takashicompany/tightwriter/images/build/IMG_2944.jpg

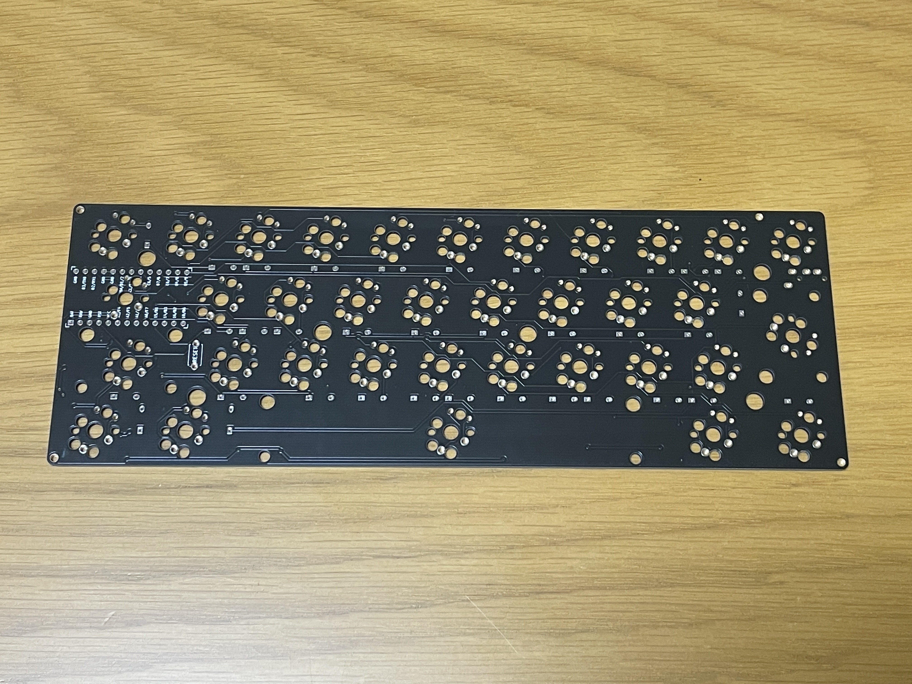
images/build/IMG_2944.jpg
