takashicompany/tightwriter/images/build/IMG_2945.jpg

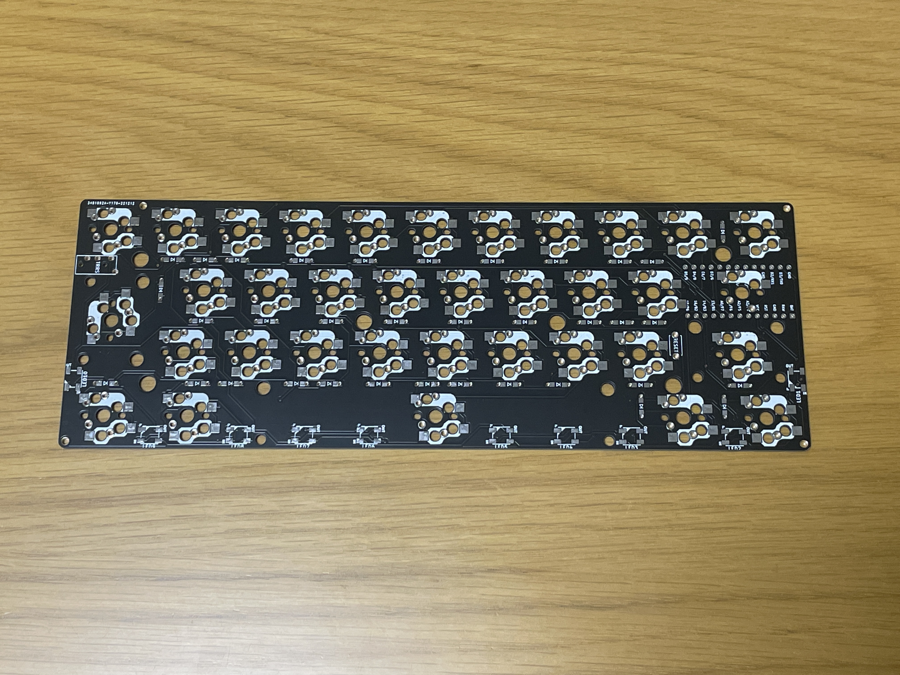
images/build/IMG_2945.jpg
