takashicompany/tightwriter/images/build/IMG_2948.jpg

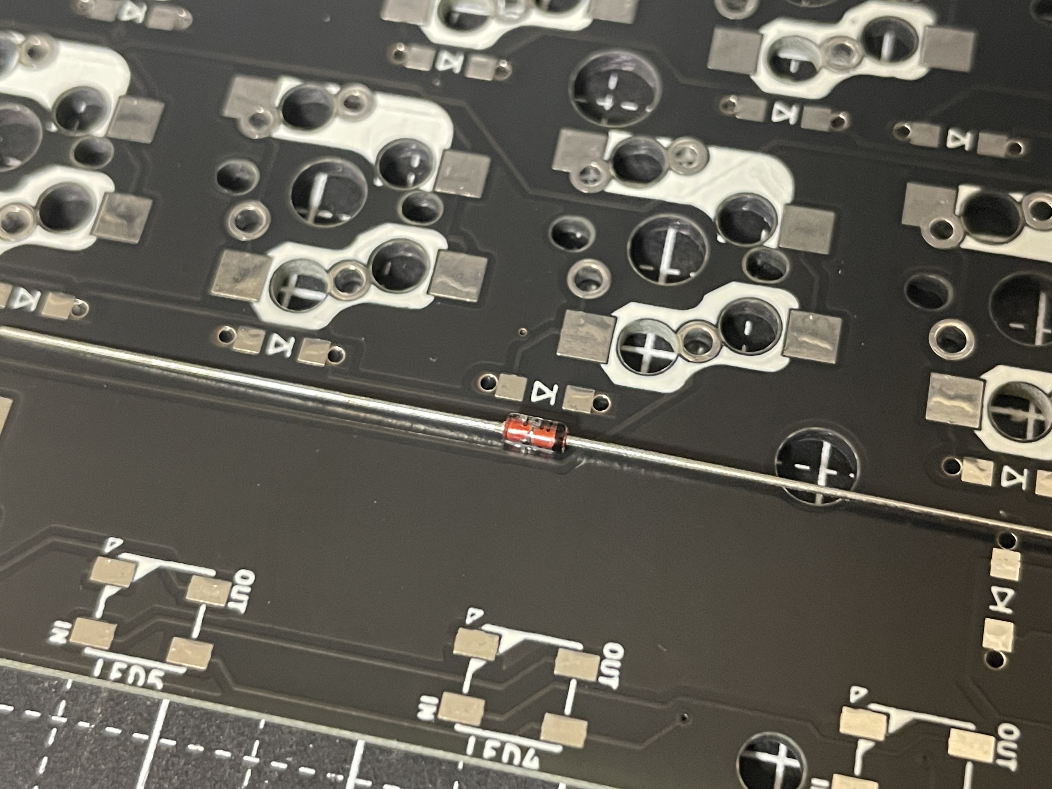
images/build/IMG_2948.jpg
