takashicompany/tightwriter/images/build/IMG_2955.jpg

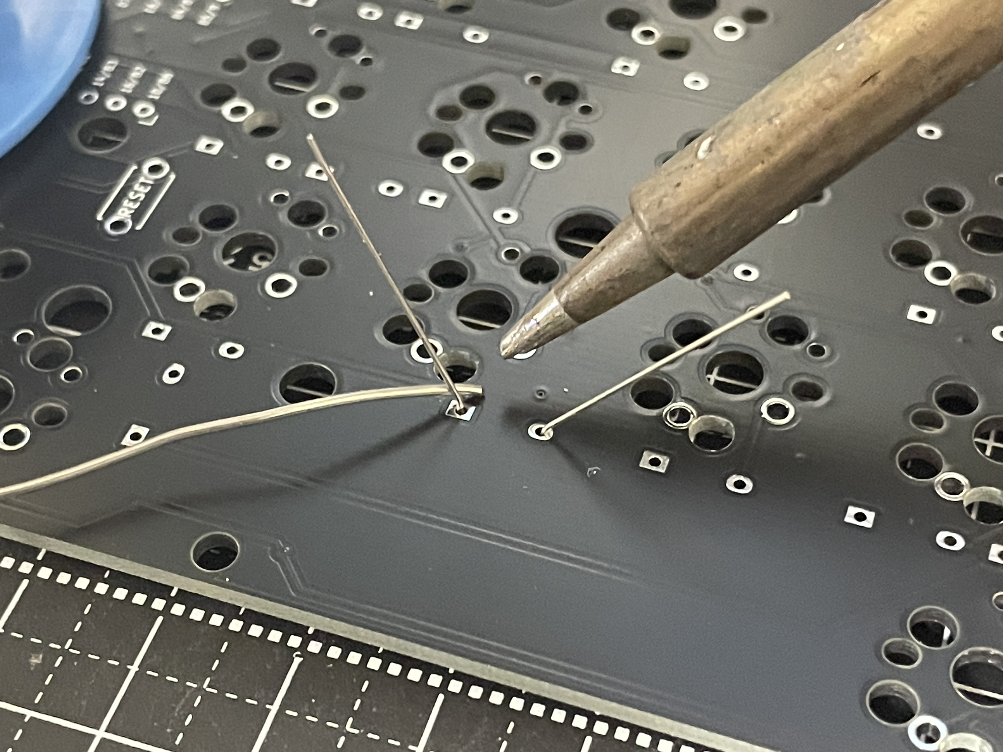
images/build/IMG_2955.jpg
