takashicompany/tightwriter/images/build/IMG_2965.jpg

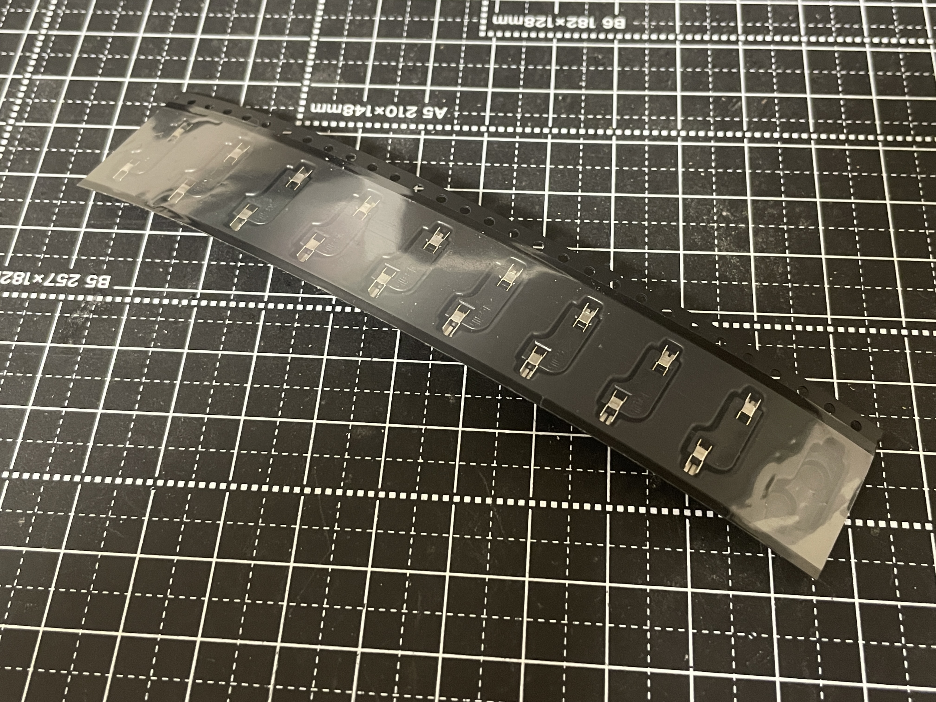
images/build/IMG_2965.jpg
