takashicompany/tightwriter/images/build/IMG_2968.jpg

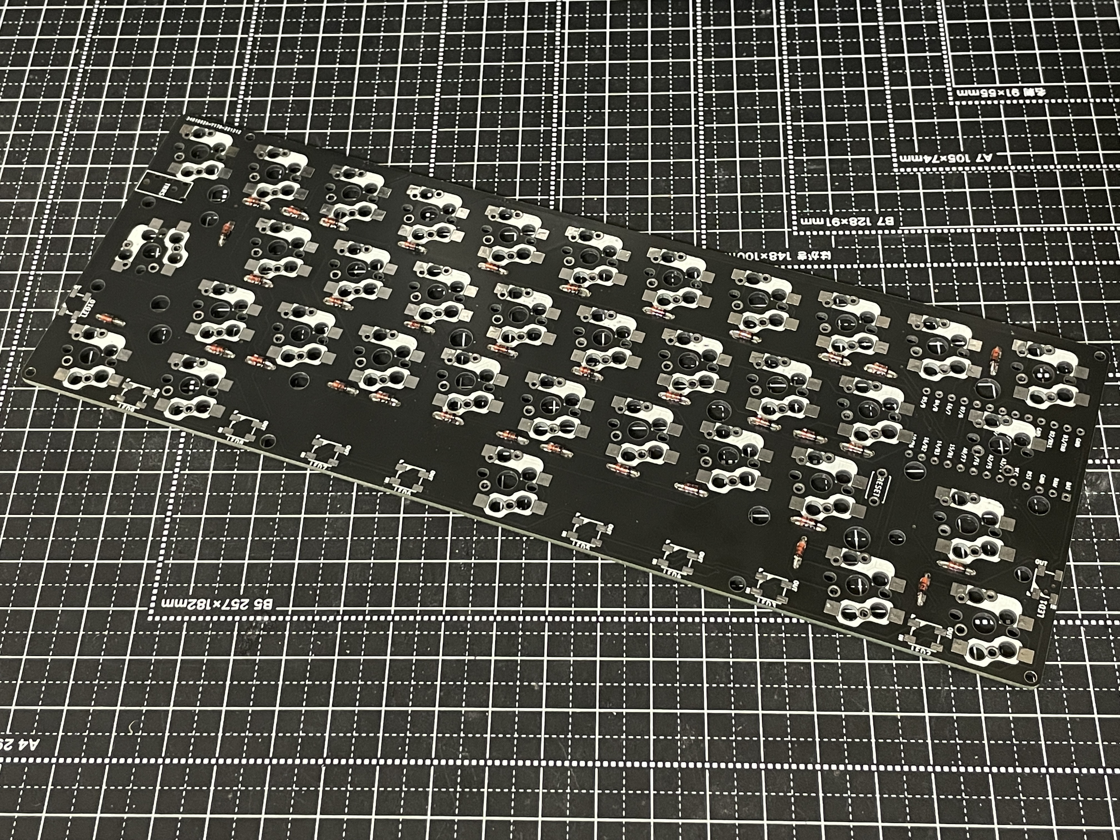
images/build/IMG_2968.jpg
