takashicompany/tightwriter/images/build/IMG_3021.jpg

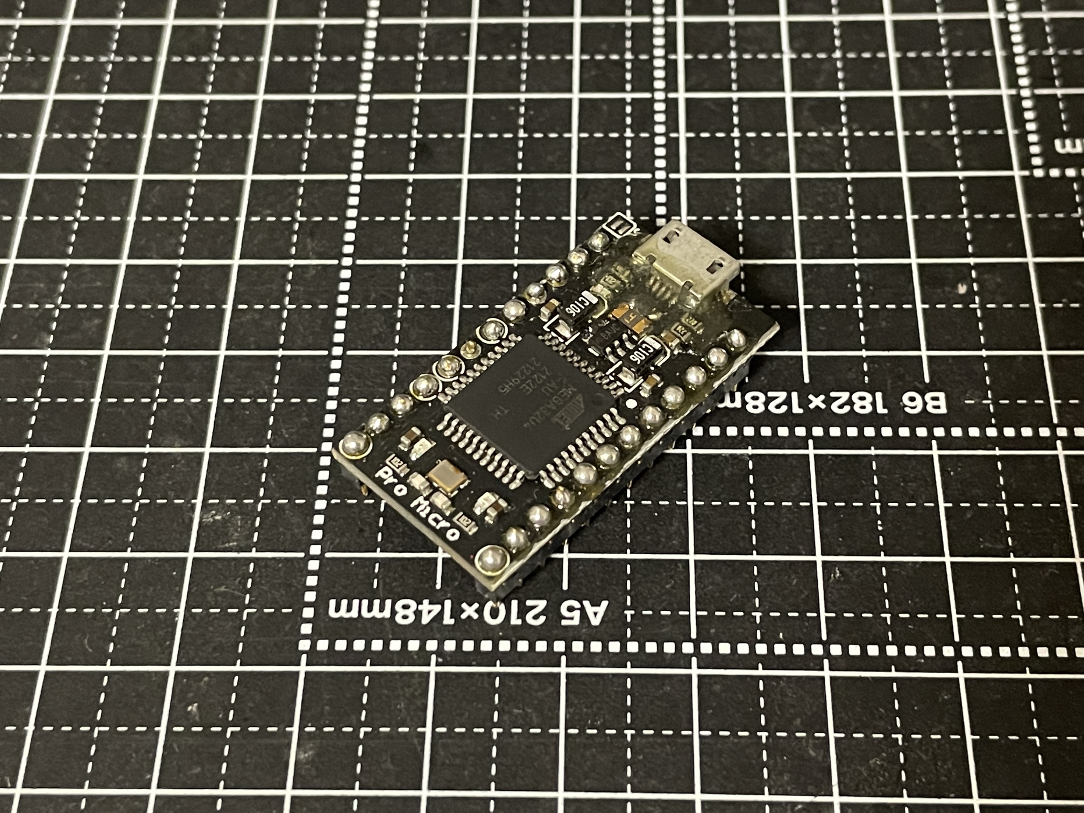
images/build/IMG_3021.jpg
