takashicompany/tightwriter/images/build/IMG_3022.jpg

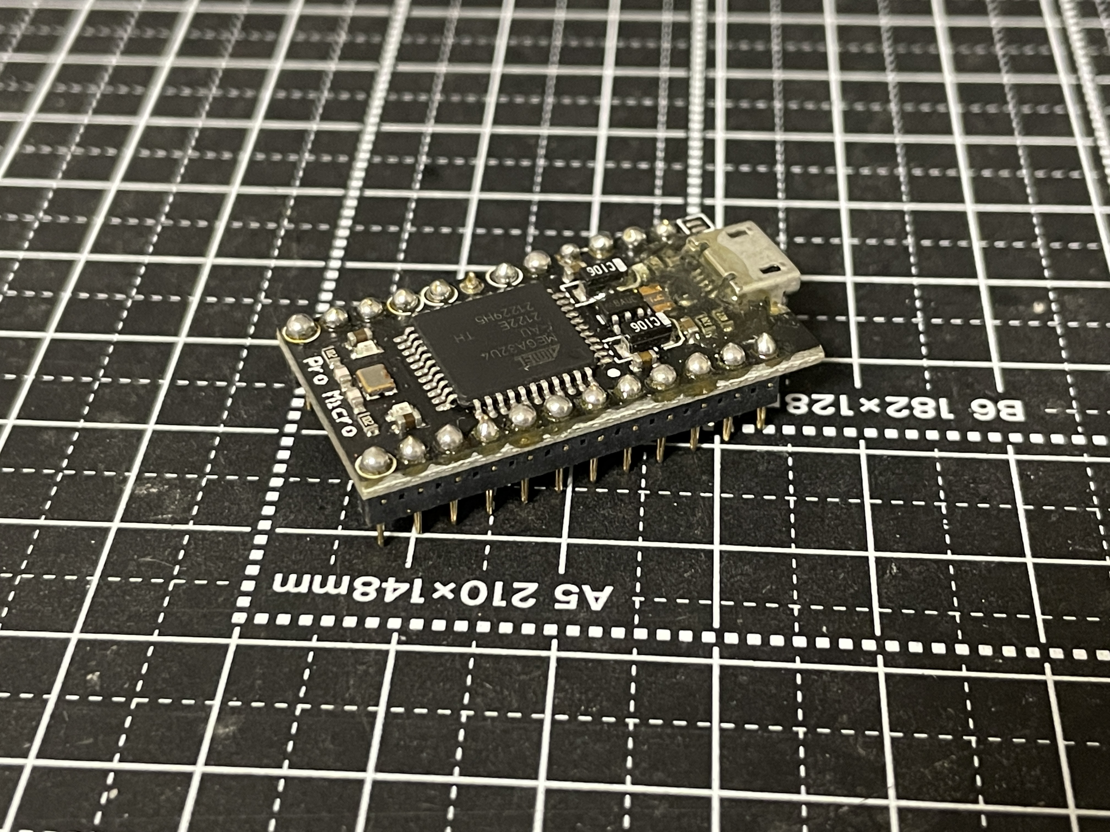
images/build/IMG_3022.jpg
