takashicompany/tightwriter/images/build/IMG_3026.jpg

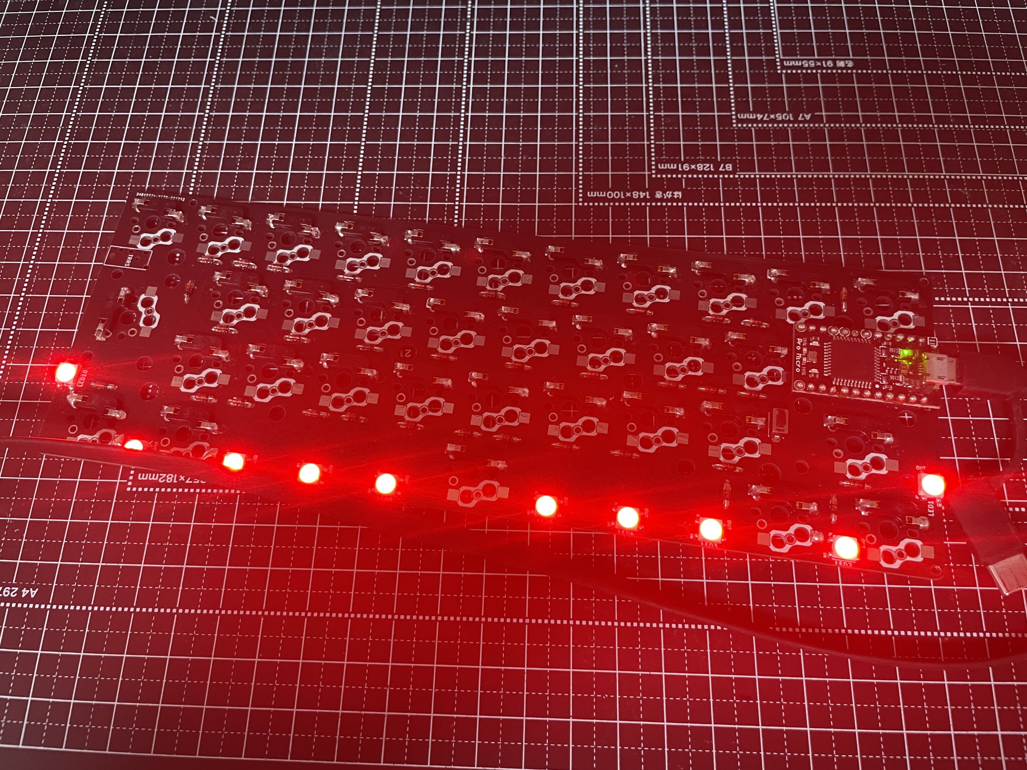
images/build/IMG_3026.jpg
