takashicompany/tightwriter/images/build/IMG_3027.jpg

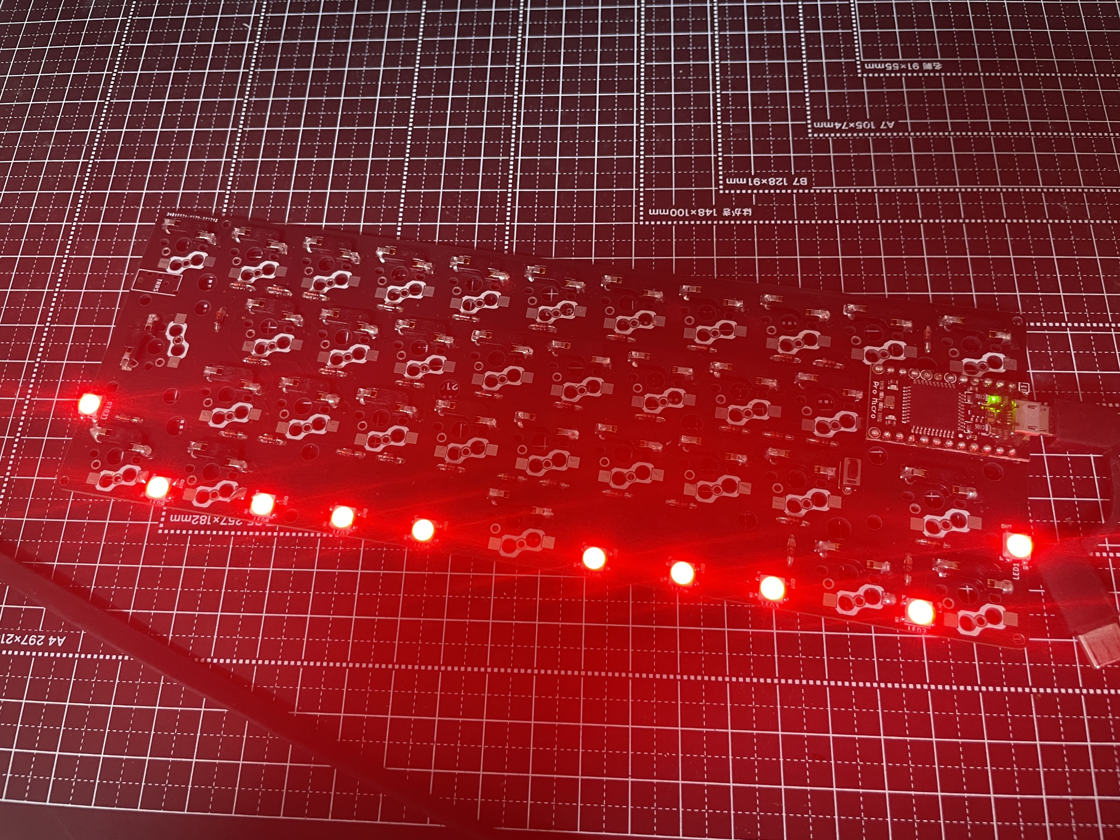
images/build/IMG_3027.jpg
