takashicompany/tightwriter/images/build/IMG_3028.jpg

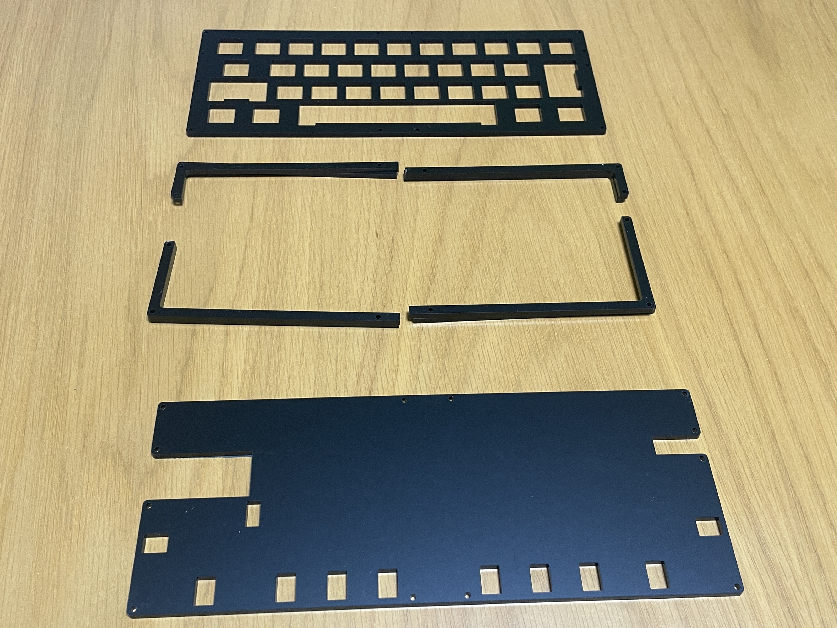
images/build/IMG_3028.jpg
