takashicompany/tightwriter/images/build/IMG_3031.jpg

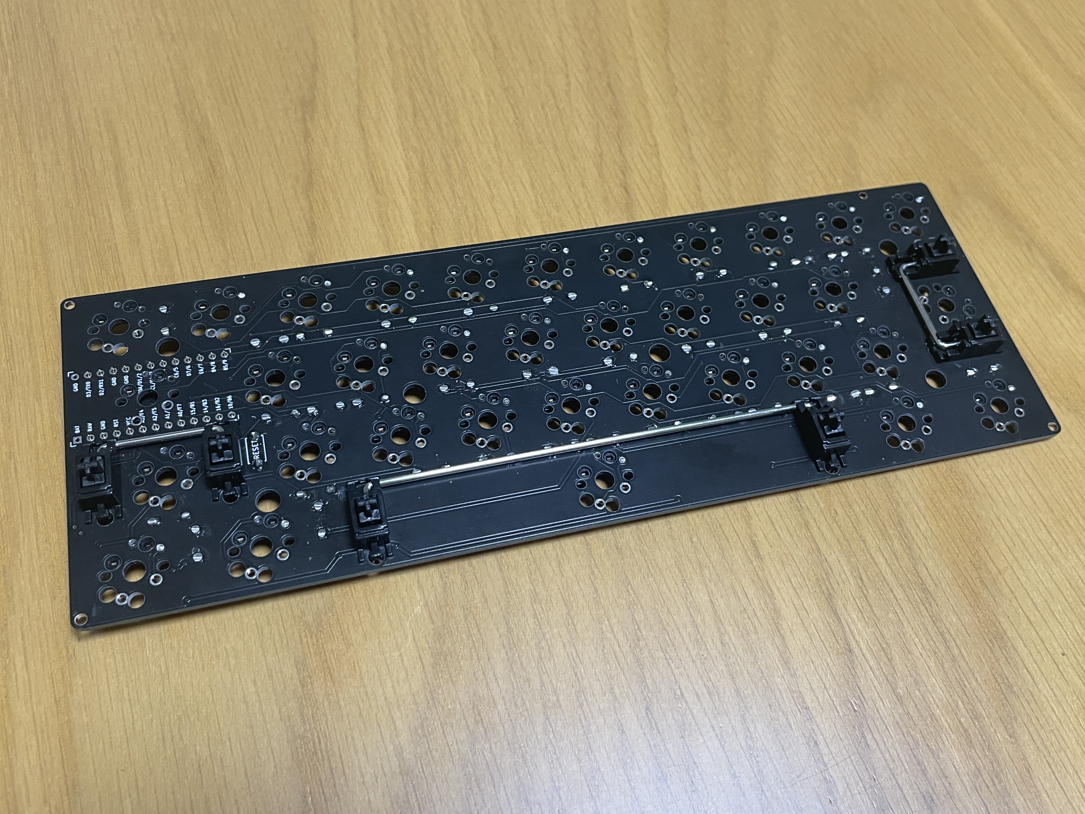
images/build/IMG_3031.jpg
