takashicompany/tightwriter/images/build/IMG_3033.jpg

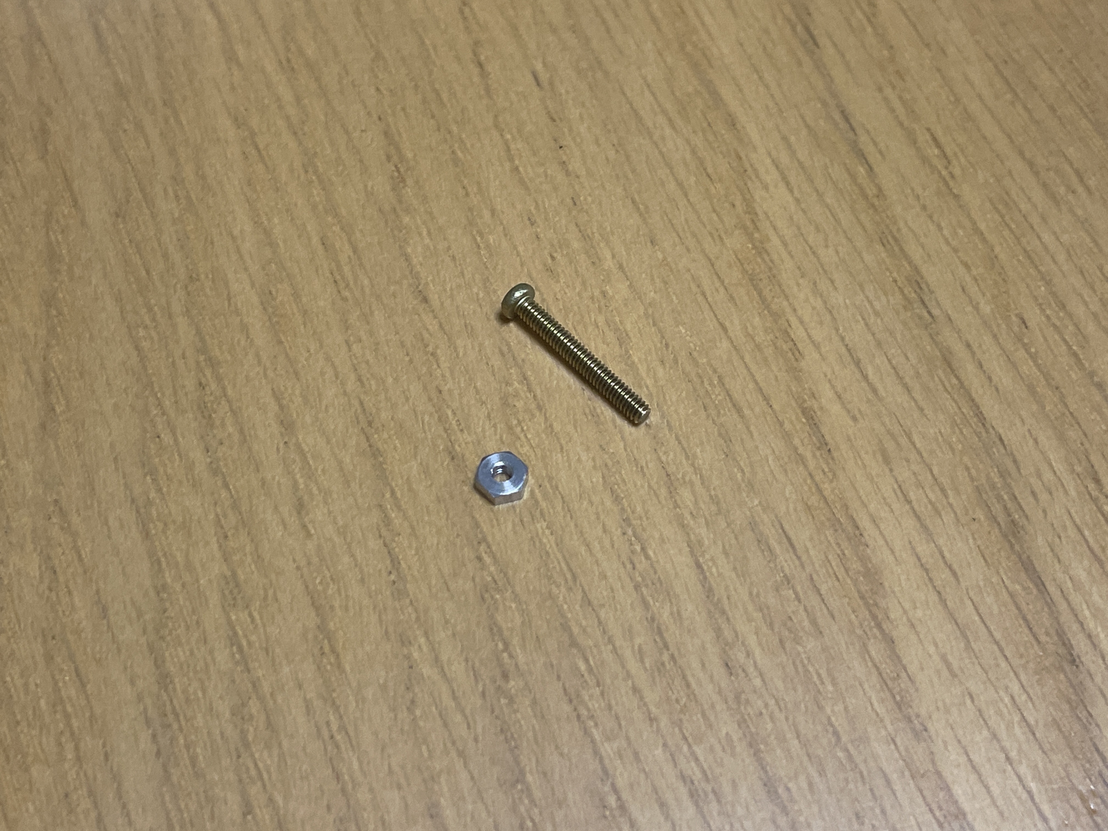
images/build/IMG_3033.jpg
