takashicompany/tightwriter/images/build/IMG_3039.jpg

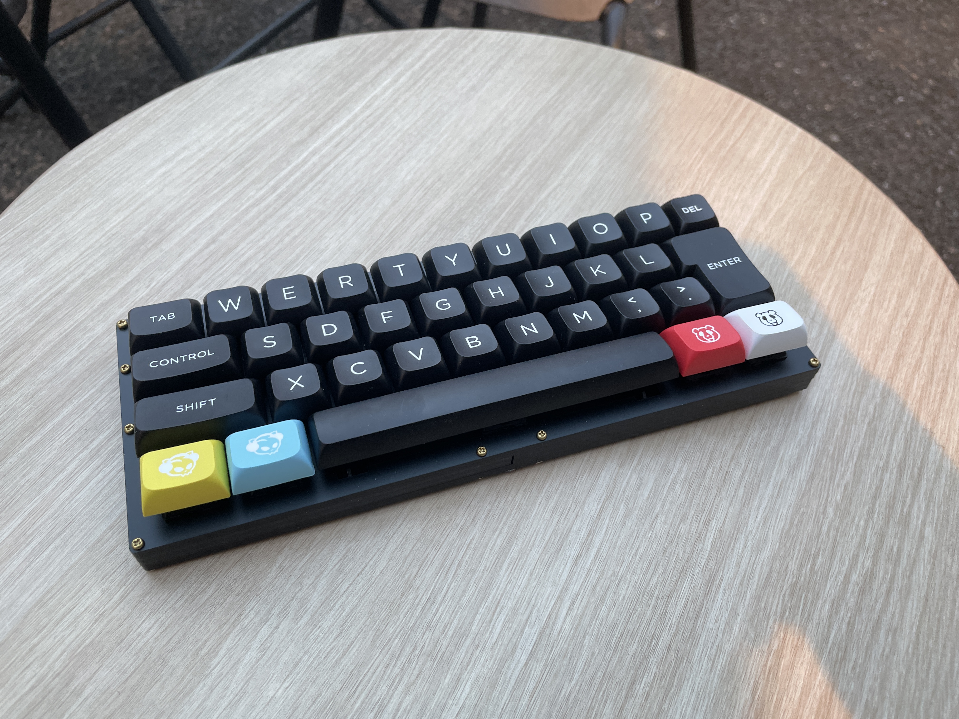
images/build/IMG_3039.jpg
