takashicompany/tightwriter/images/build/IMG_3040.jpg

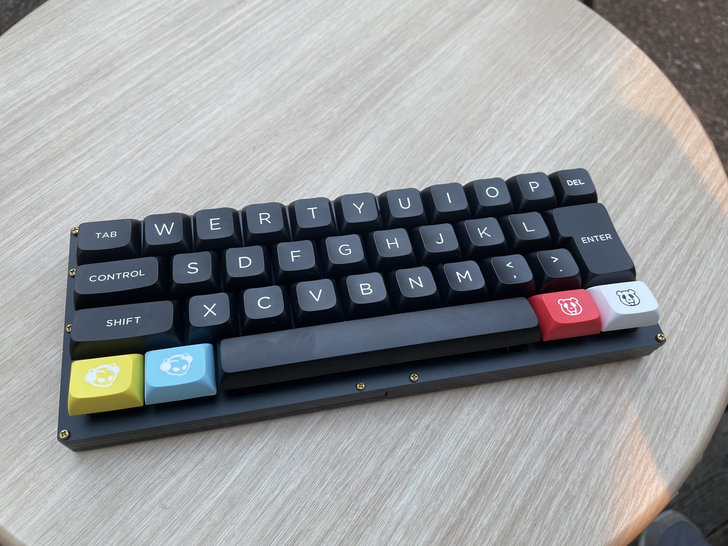
images/build/IMG_3040.jpg
