takashicompany/tightwriter/images/build/IMG_3042.jpg

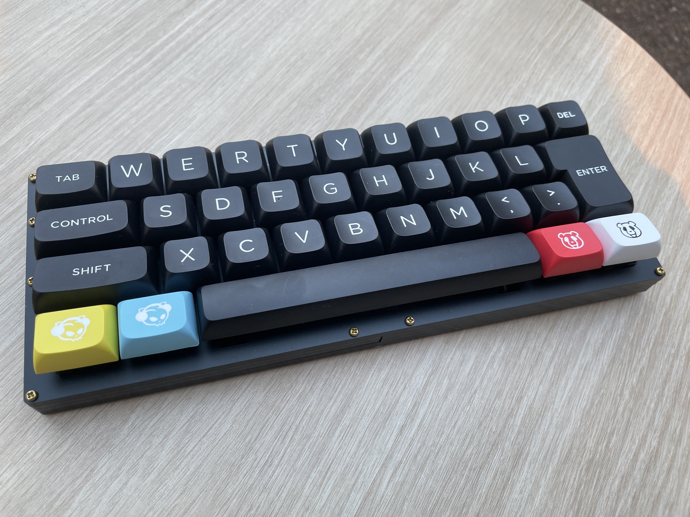
images/build/IMG_3042.jpg
