takashicompany/tightwriter/images/build/IMG_3043.jpg

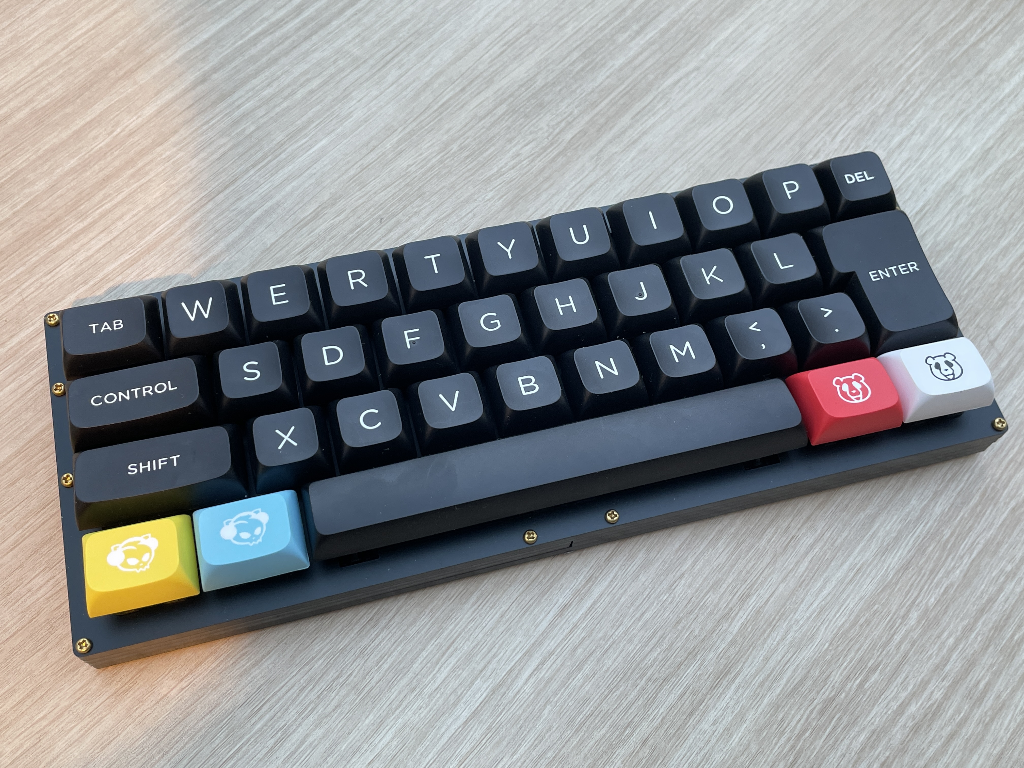
images/build/IMG_3043.jpg
