takashicompany/tightwriter/images/build/IMG_3044.jpg

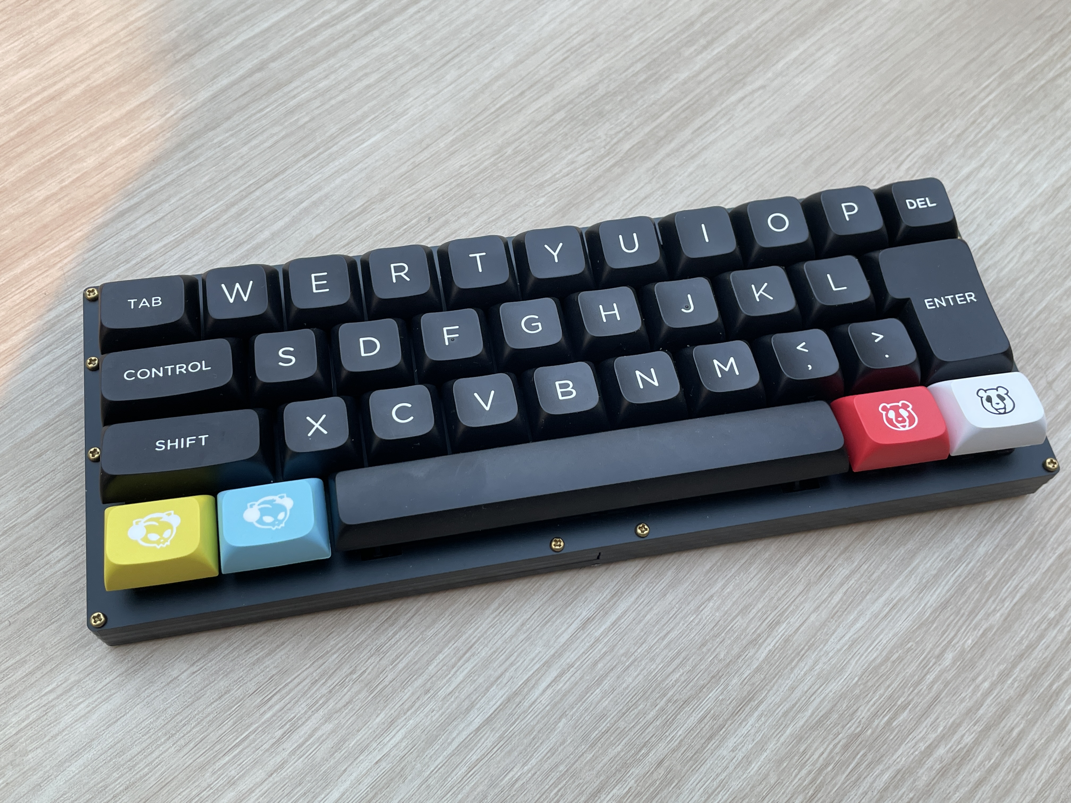
images/build/IMG_3044.jpg
