takashicompany/tightwriter/images/build/IMG_3045.jpg

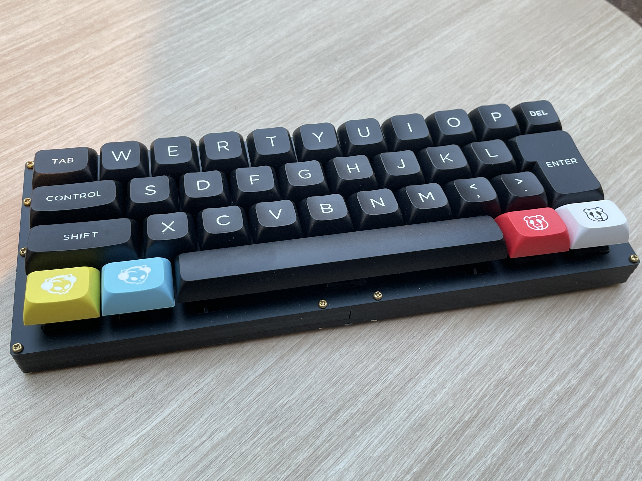
images/build/IMG_3045.jpg
