takashicompany/tightwriter/images/build/IMG_3057.jpg

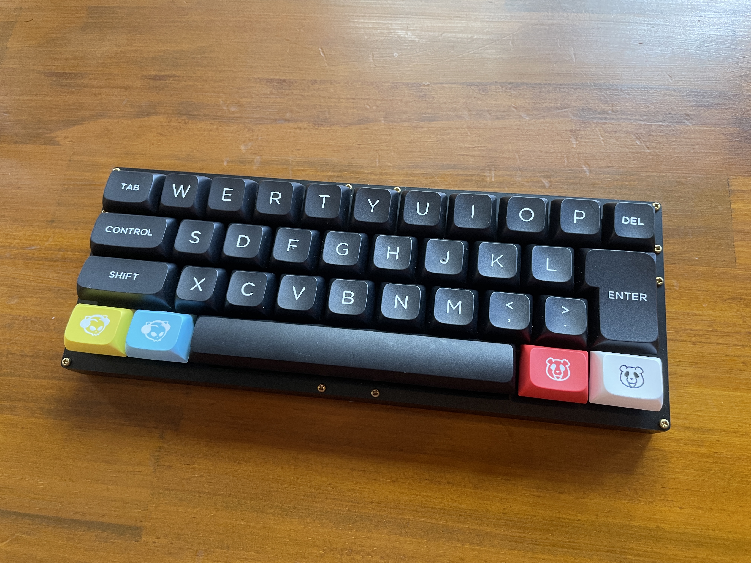
images/build/IMG_3057.jpg
