takashicompany/tightwriter/images/build/IMG_3058.jpg

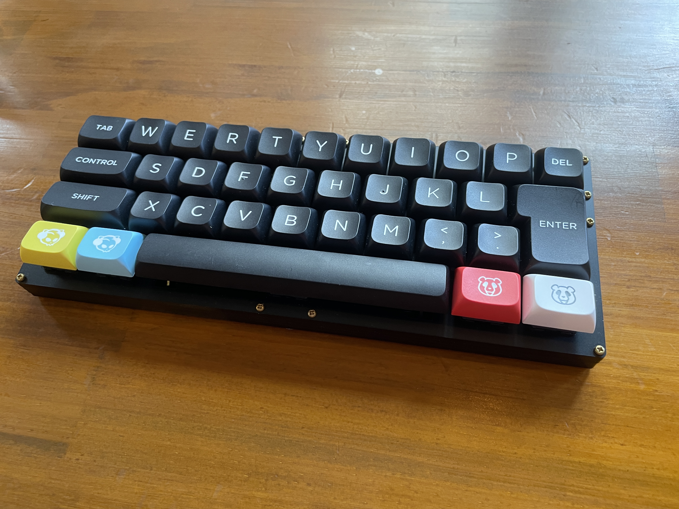
images/build/IMG_3058.jpg
