takashicompany/tightwriter/images/build/IMG_3059.jpg

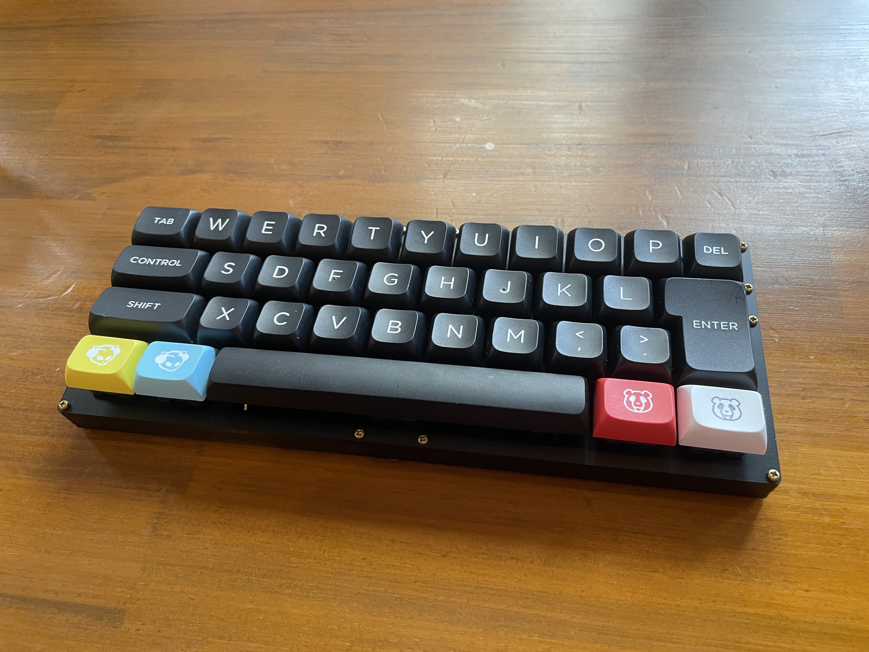
images/build/IMG_3059.jpg
