takashicompany/tightwriter/images/build/IMG_3060.jpg

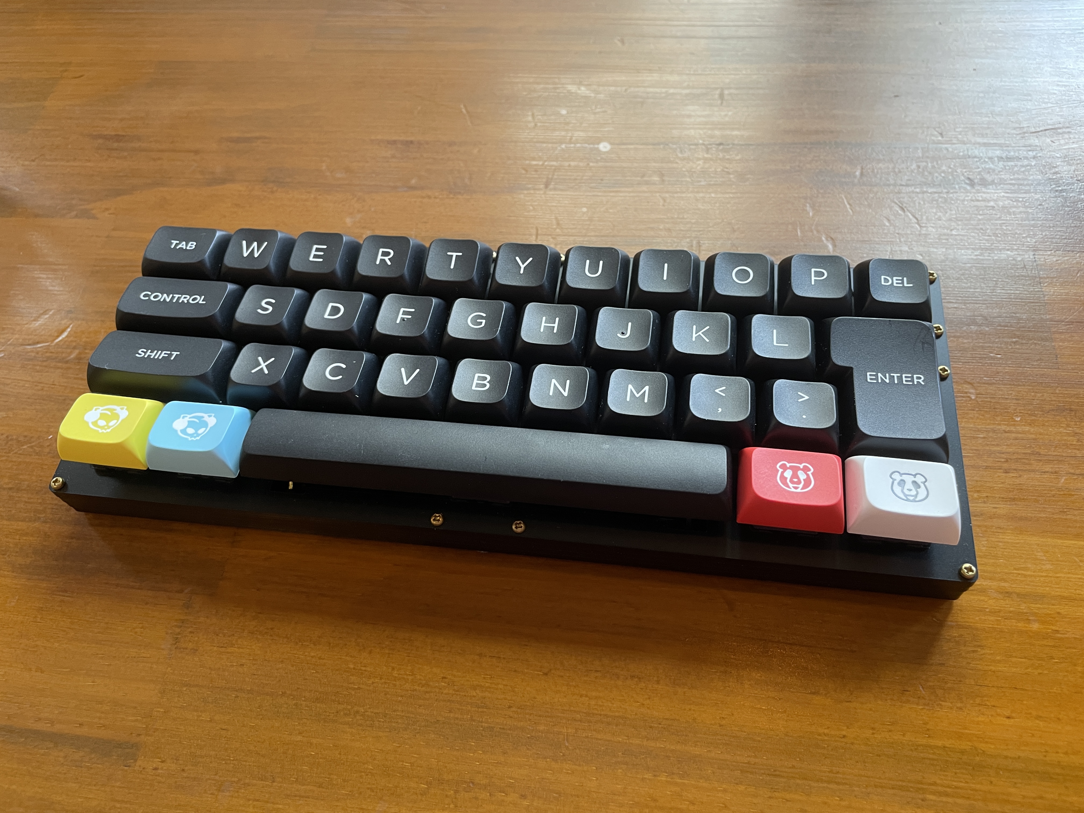
images/build/IMG_3060.jpg
