takashicompany/tightwriter/images/build/IMG_3132.jpg

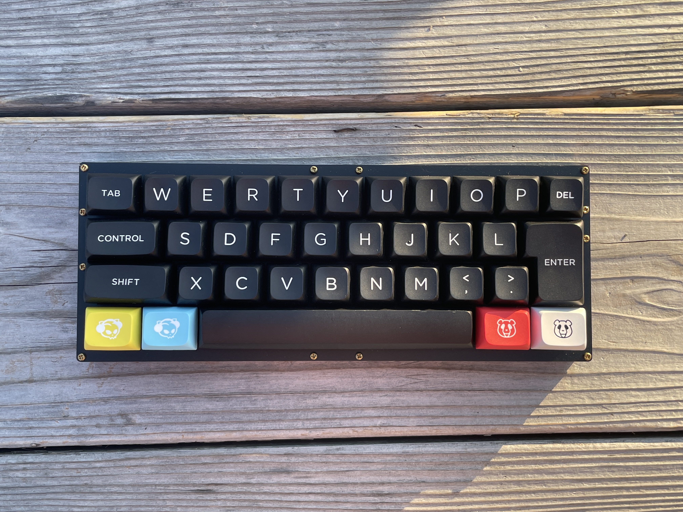
images/build/IMG_3132.jpg
