takashicompany/tightwriter/images/build/IMG_3134.jpg

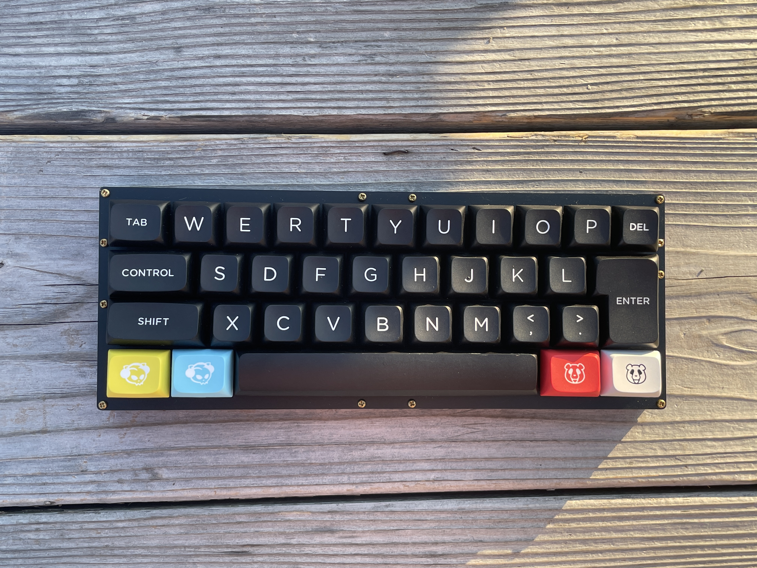
images/build/IMG_3134.jpg
