takashicompany/tightwriter/images/build/IMG_3135.jpg

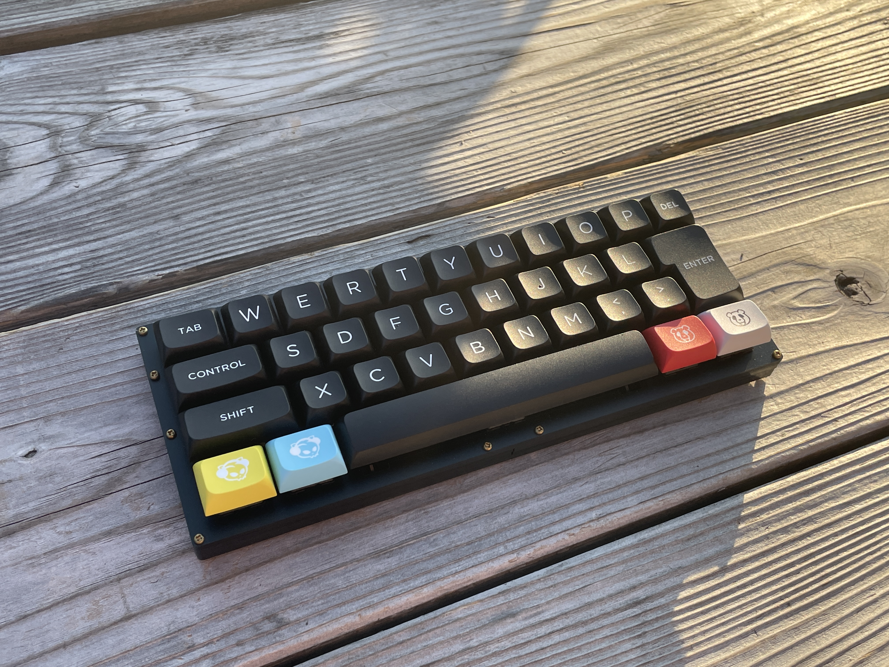
images/build/IMG_3135.jpg
