takashicompany/tightwriter/images/build/IMG_3136.jpg

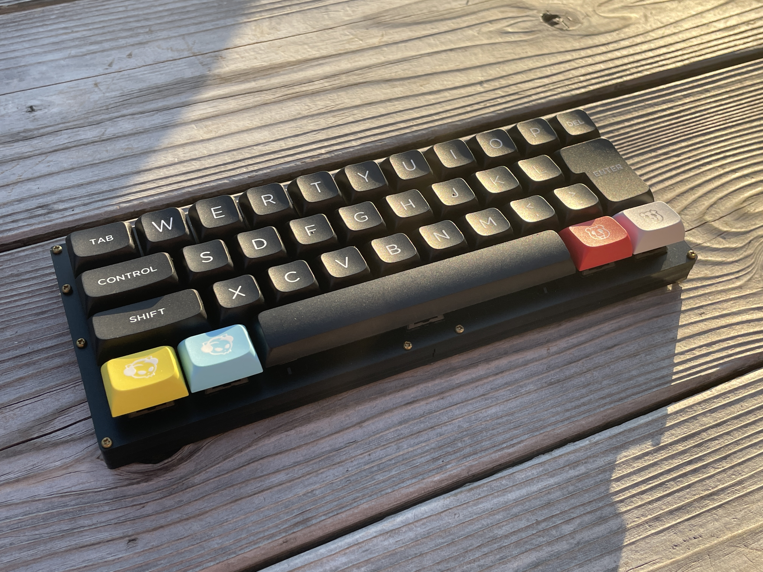
images/build/IMG_3136.jpg
