takashicompany/tightwriter/images/build/IMG_3137.jpg

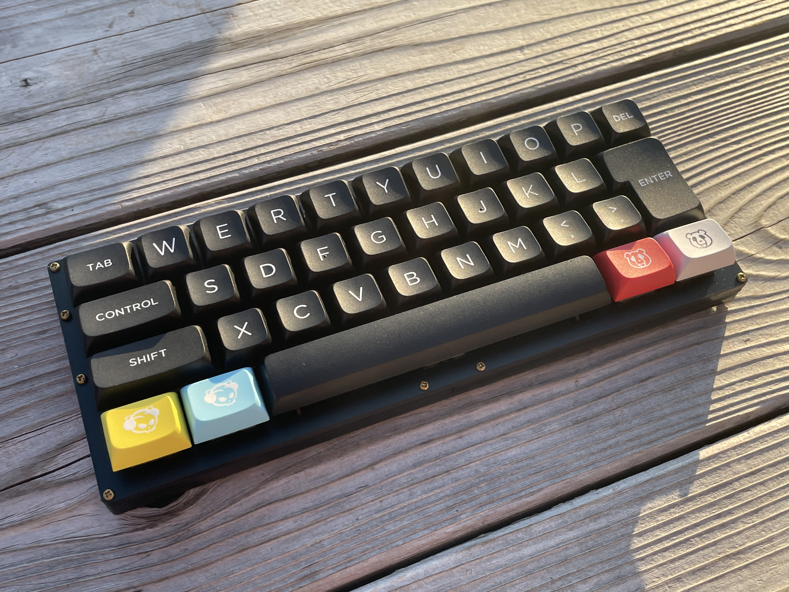
images/build/IMG_3137.jpg
