takashicompany/tightwriter/images/build/IMG_3139.jpg

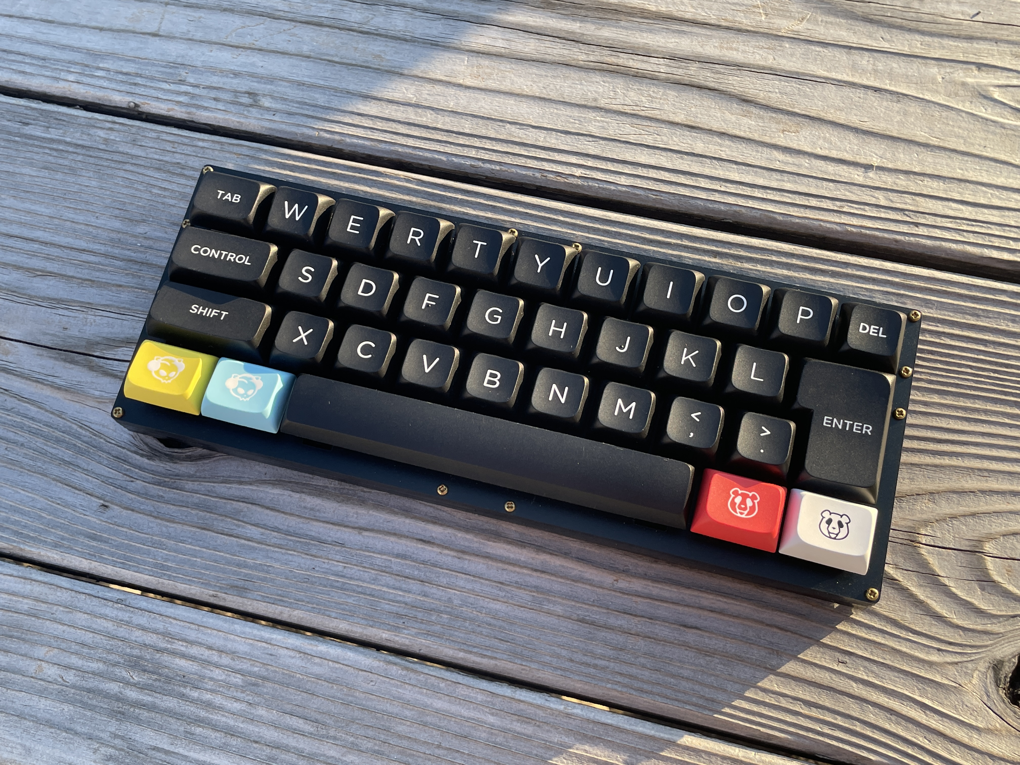
images/build/IMG_3139.jpg
