takashicompany/tightwriter/images/build/IMG_3140.jpg

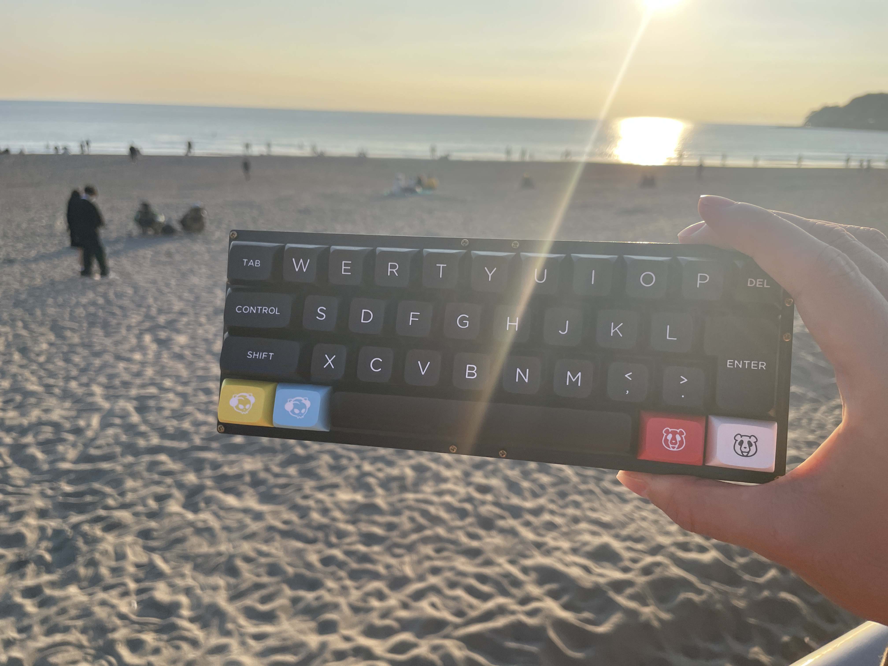
images/build/IMG_3140.jpg
