takashicompany/tightwriter/images/build/IMG_3141.jpg

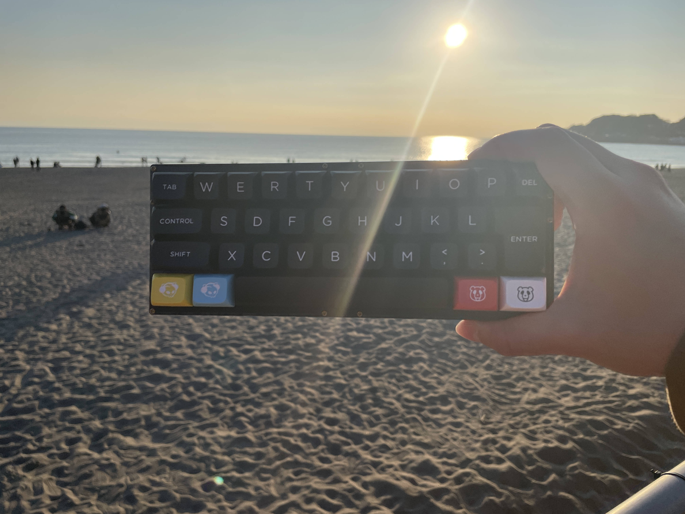
images/build/IMG_3141.jpg
