takashicompany/tightwriter/images/build/IMG_3142.jpg

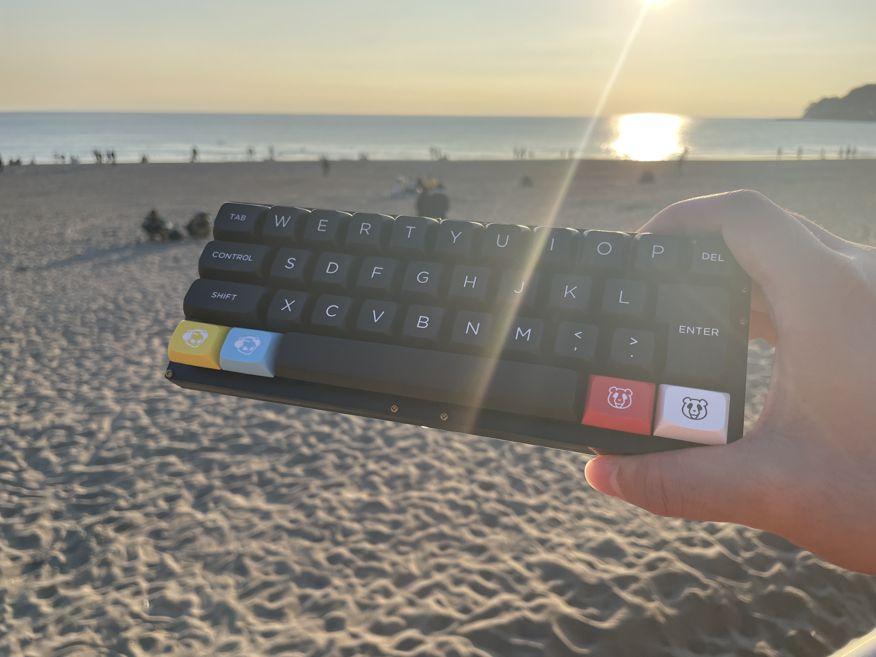
images/build/IMG_3142.jpg
