takashicompany/tightwriter/images/build/IMG_3144.jpg

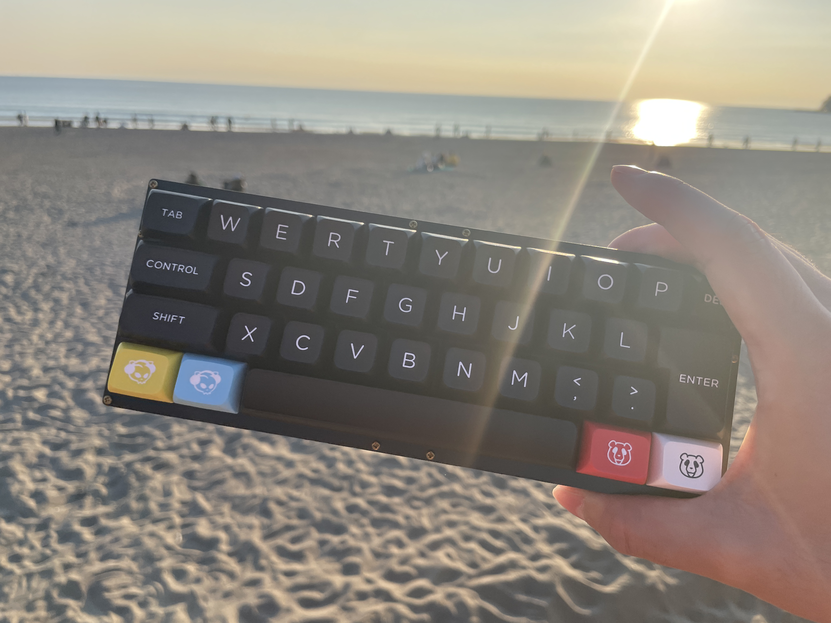
images/build/IMG_3144.jpg
