takashicompany/tightwriter/images/build/IMG_3145.jpg

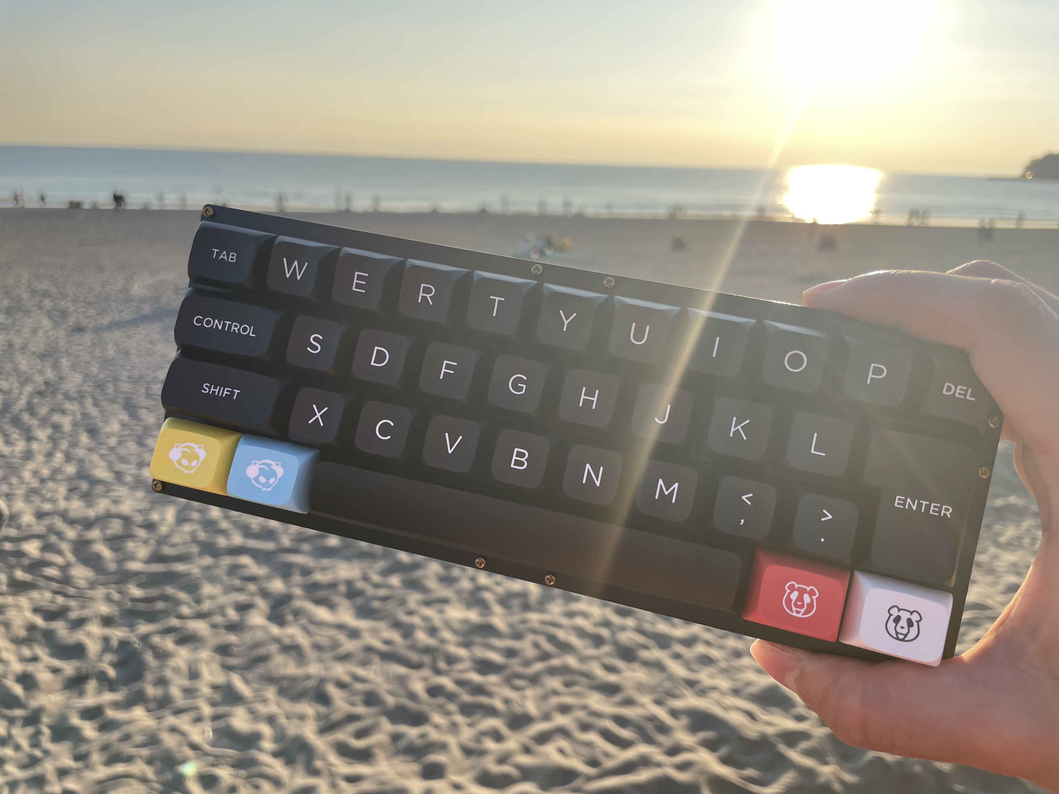
images/build/IMG_3145.jpg
