takashicompany/tightwriter/images/build/IMG_3146.jpg

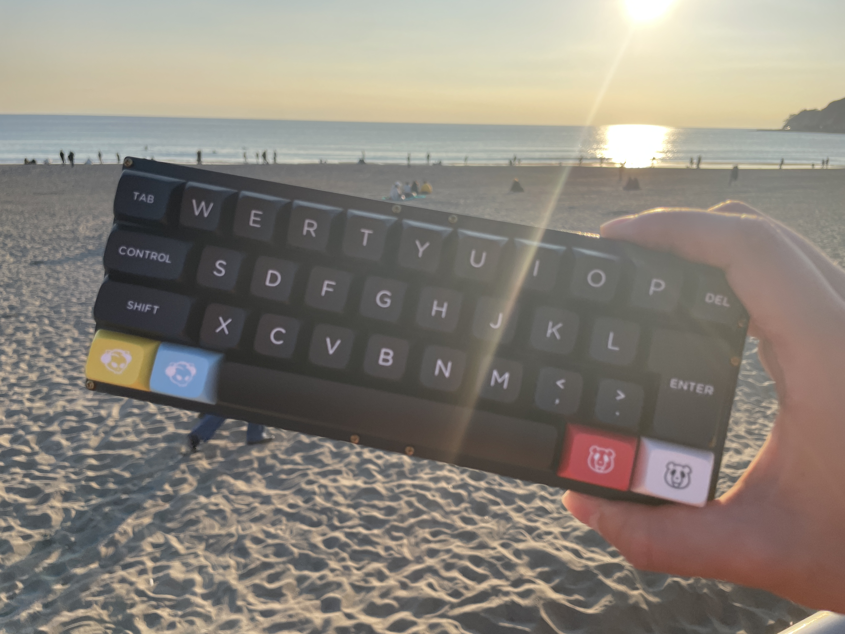
images/build/IMG_3146.jpg
