takashicompany/tightwriter/images/build/IMG_3148.jpg

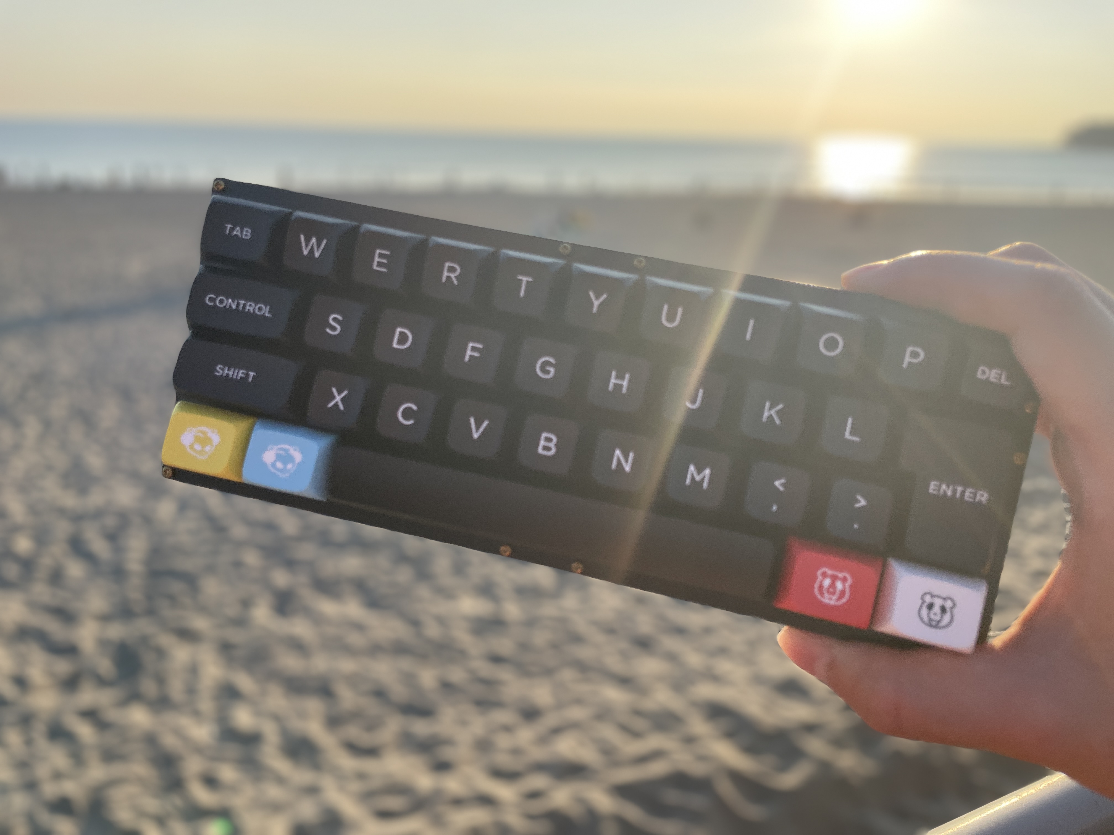
images/build/IMG_3148.jpg
