takashicompany/tightwriter/images/build/IMG_3149.jpg

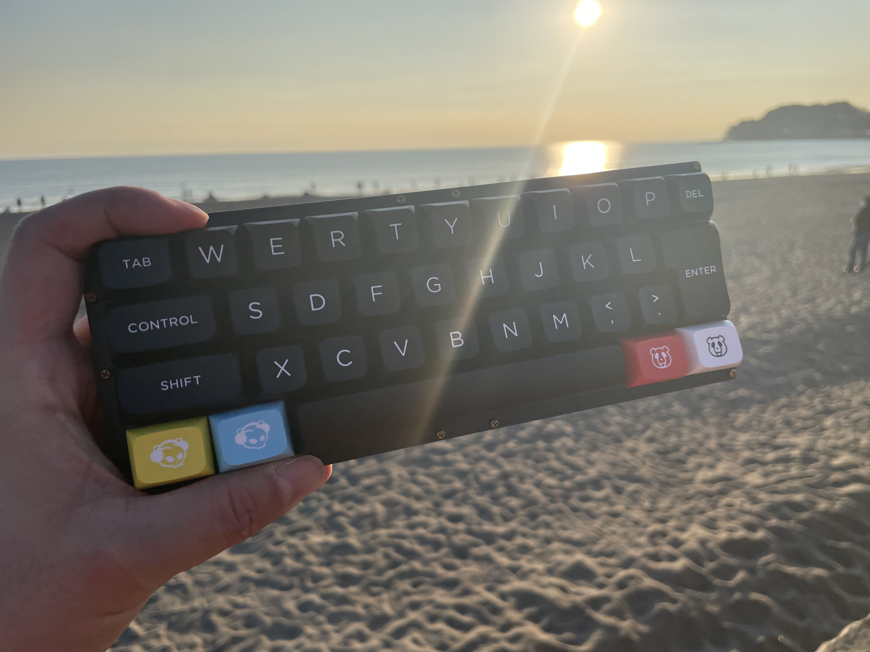
images/build/IMG_3149.jpg
