takashicompany/tightwriter/images/build/IMG_3150.jpg

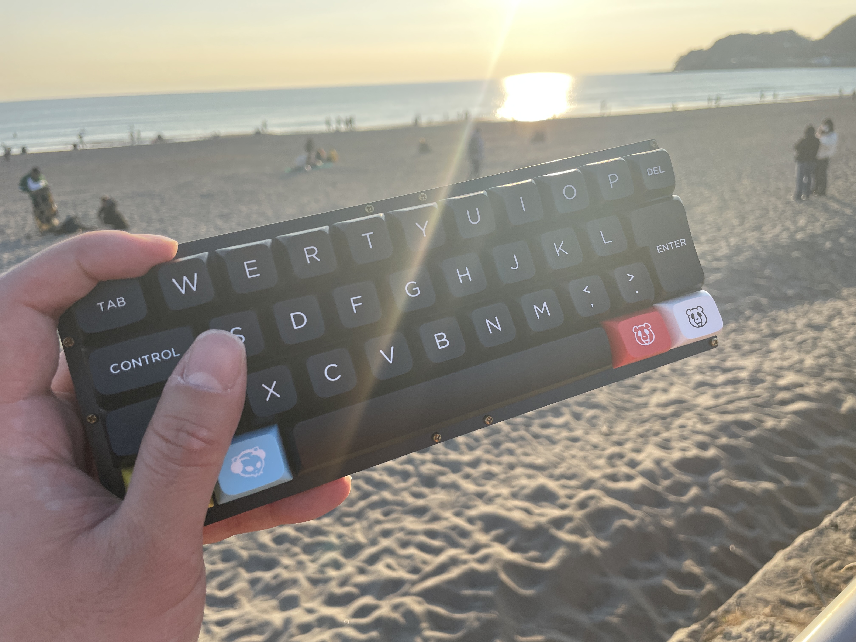
images/build/IMG_3150.jpg
