takashicompany/tightwriter/images/build/IMG_3151.jpg

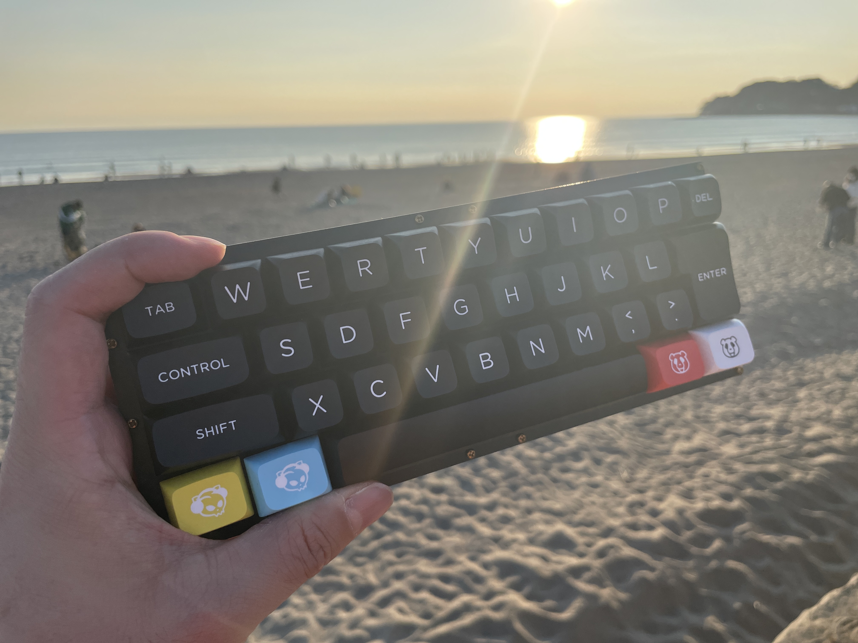
images/build/IMG_3151.jpg
