takashicompany/tightwriter/images/build/IMG_3152.jpg

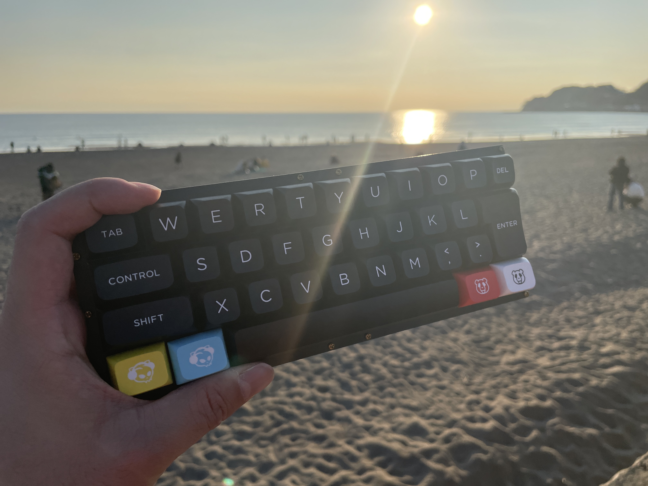
images/build/IMG_3152.jpg
