takashicompany/tightwriter/images/build/IMG_3153.jpg

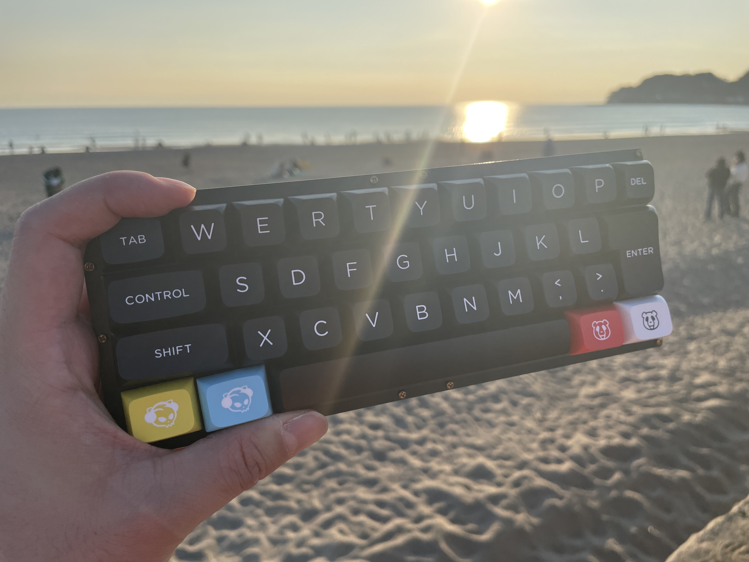
images/build/IMG_3153.jpg
