takashicompany/tightwriter/images/build/IMG_3154.jpg

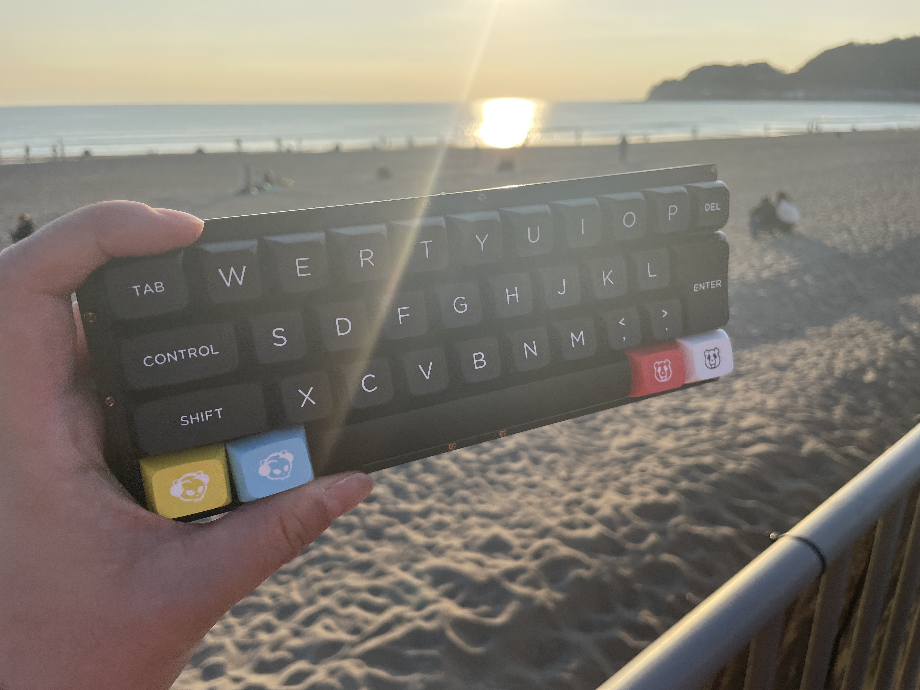
images/build/IMG_3154.jpg
