takashicompany/tightwriter/images/build/IMG_3156.jpg

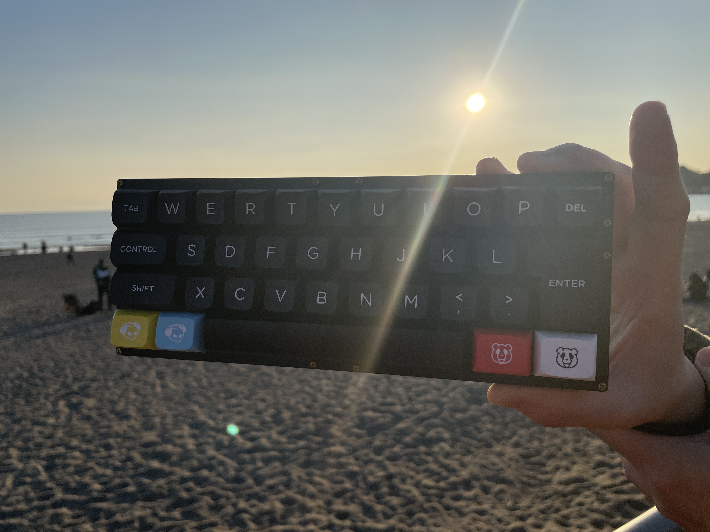
images/build/IMG_3156.jpg
