takashicompany/tightwriter/images/build/IMG_3157.jpg

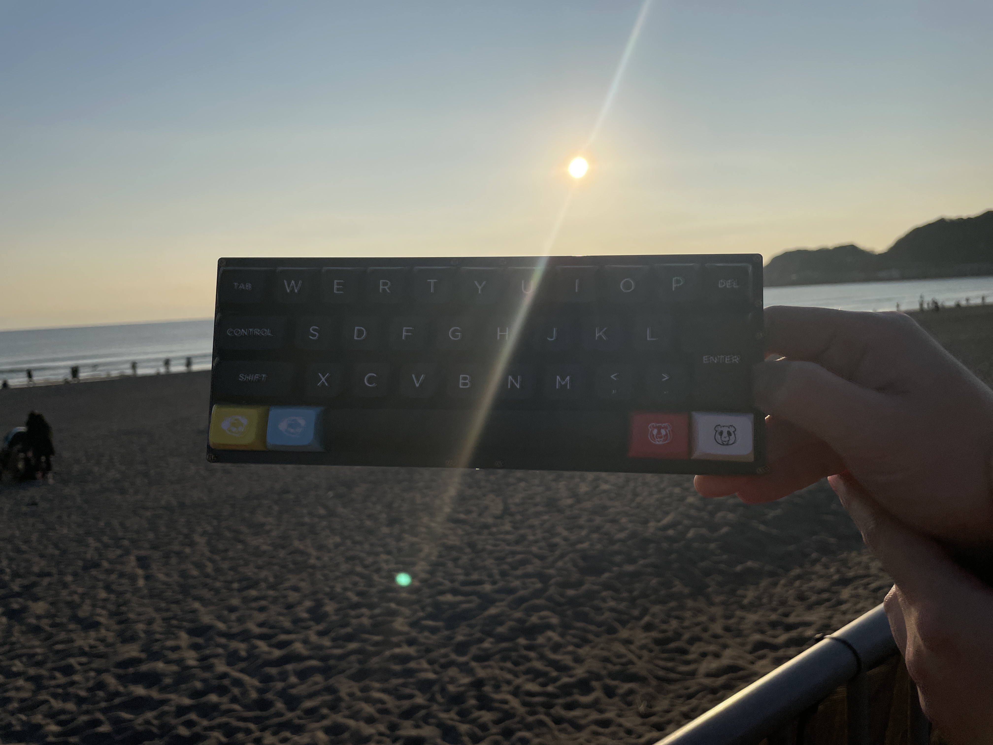
images/build/IMG_3157.jpg
