takashicompany/tightwriter/images/build/IMG_3158.jpg

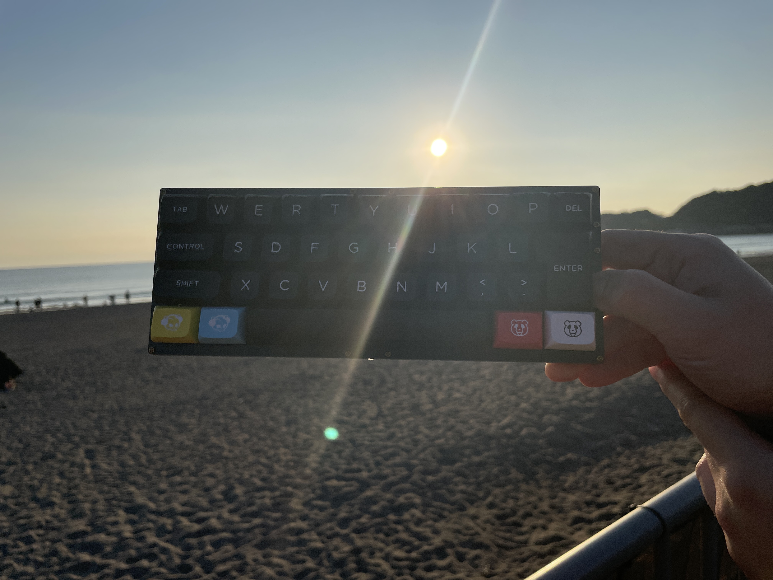
images/build/IMG_3158.jpg
