takashicompany/tightwriter/images/build/IMG_3159.jpg

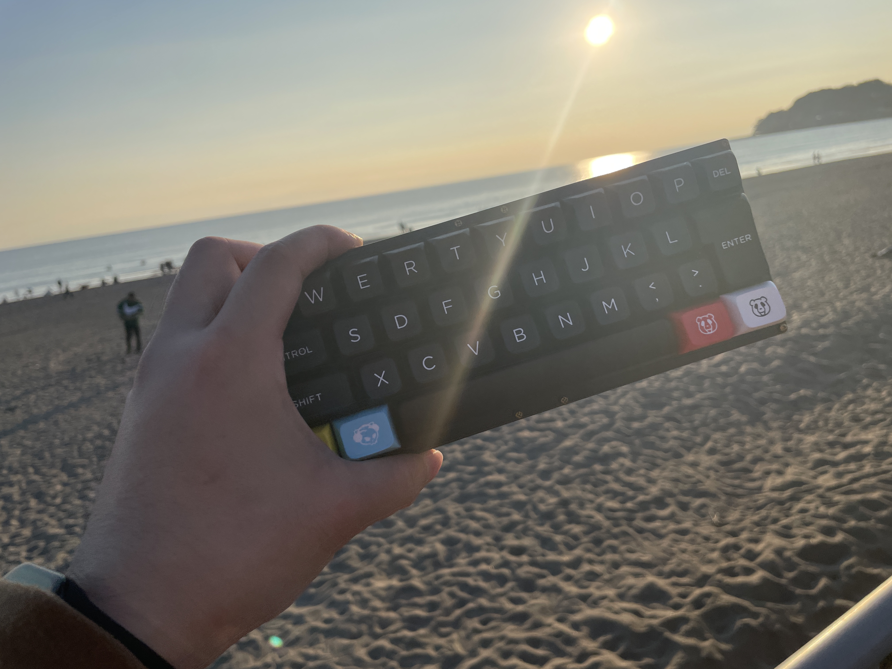
images/build/IMG_3159.jpg
