takashicompany/tightwriter/images/build/IMG_3160.jpg

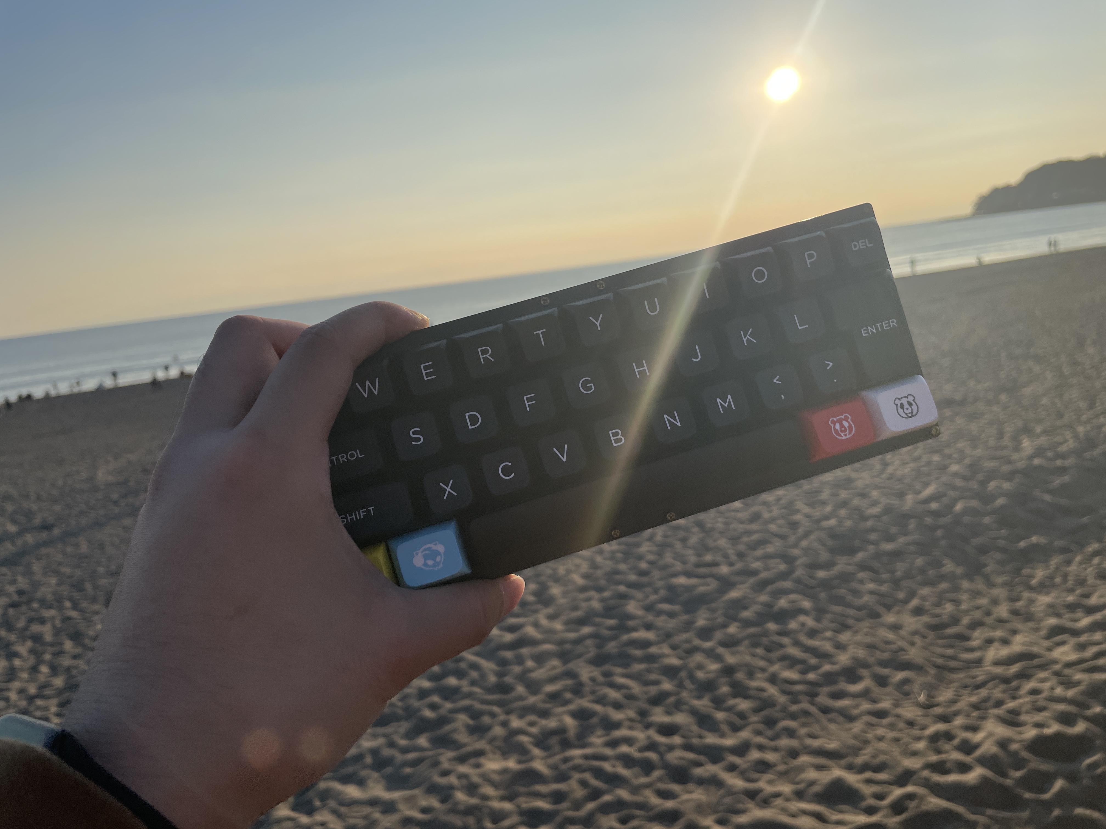
images/build/IMG_3160.jpg
