takashicompany/tightwriter/images/build/IMG_3161.jpg

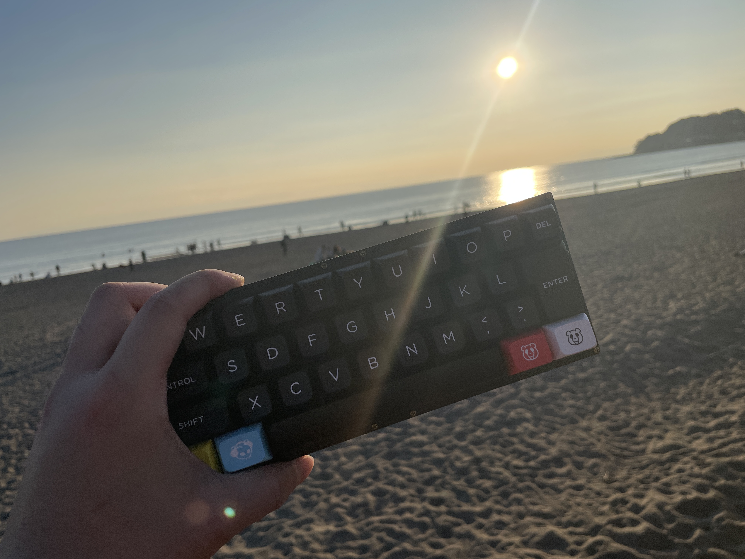
images/build/IMG_3161.jpg
