takashicompany/tightwriter/images/build/IMG_3162.jpg

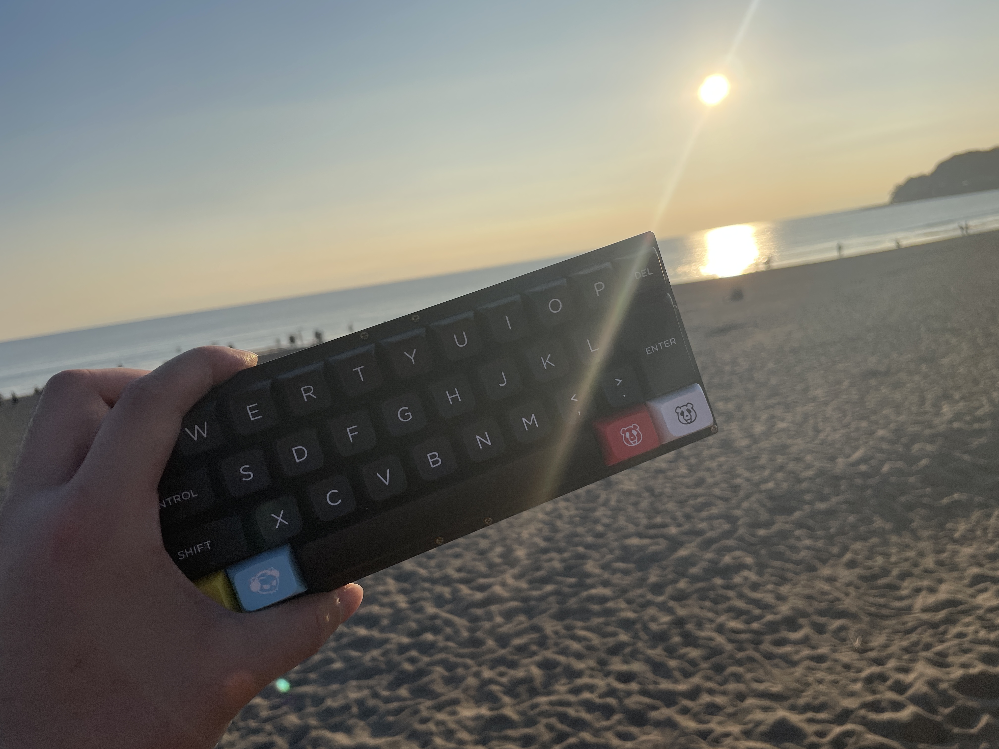
images/build/IMG_3162.jpg
