takashicompany/tightwriter/images/build/IMG_3163.jpg

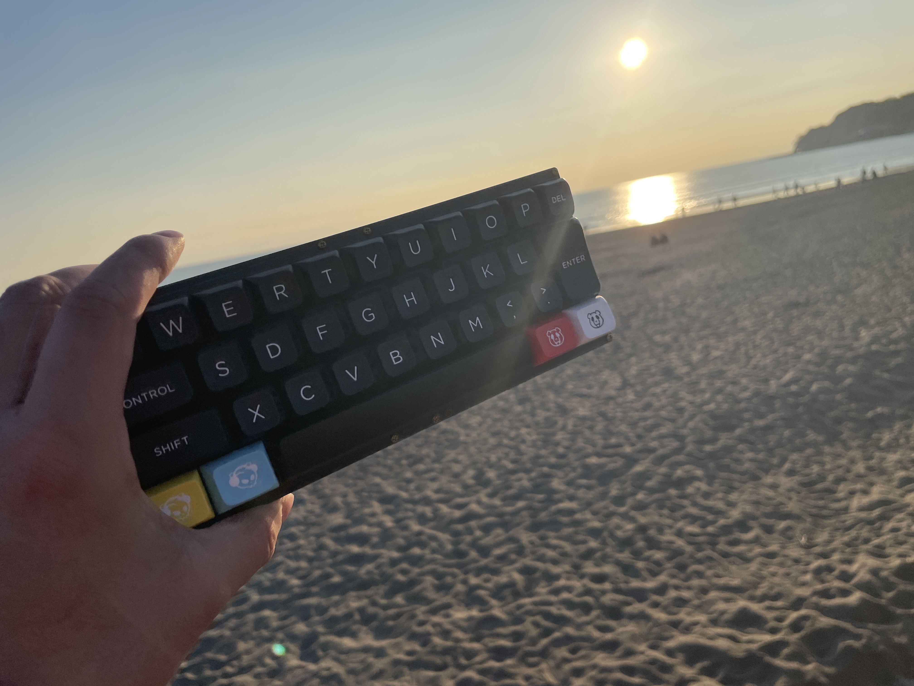
images/build/IMG_3163.jpg
