takashicompany/tightwriter/images/build/IMG_3174.jpg

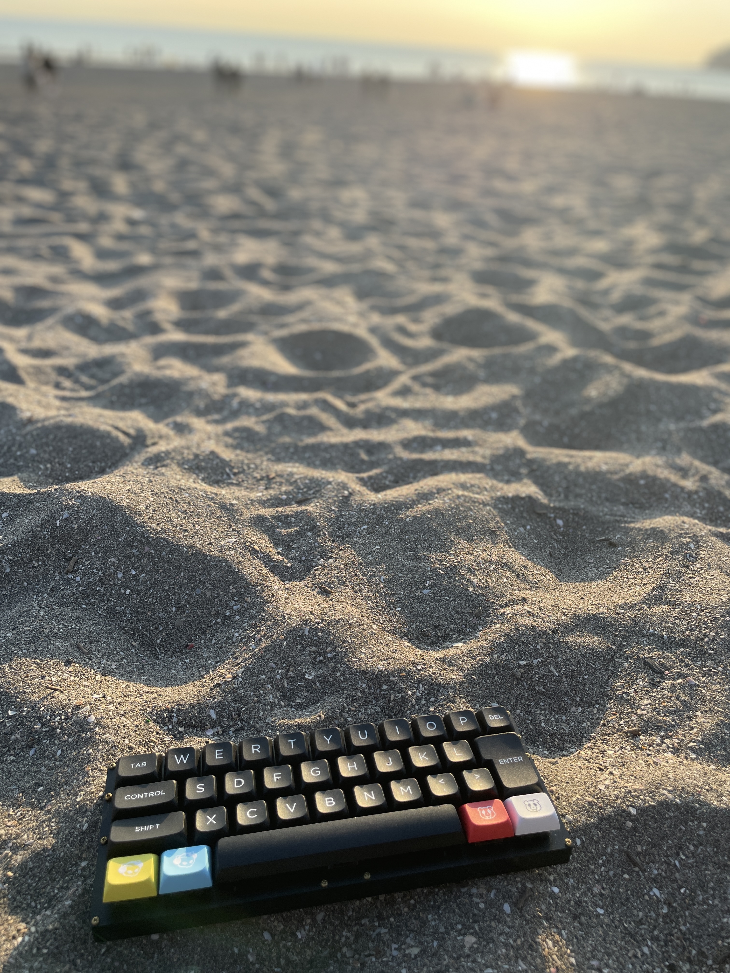
images/build/IMG_3174.jpg
