takashicompany/tightwriter/images/build/IMG_3175.jpg

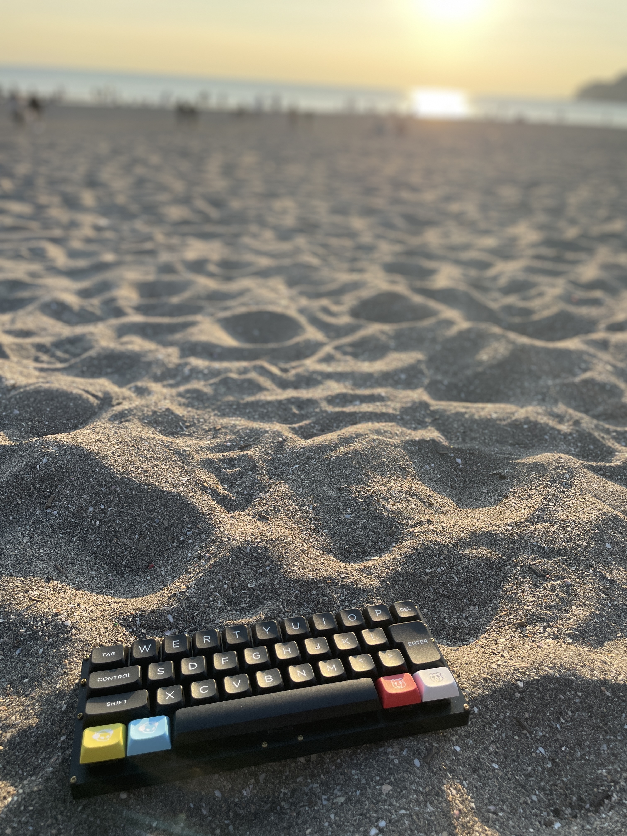
images/build/IMG_3175.jpg
