takashicompany/tightwriter/images/build/IMG_3176.jpg

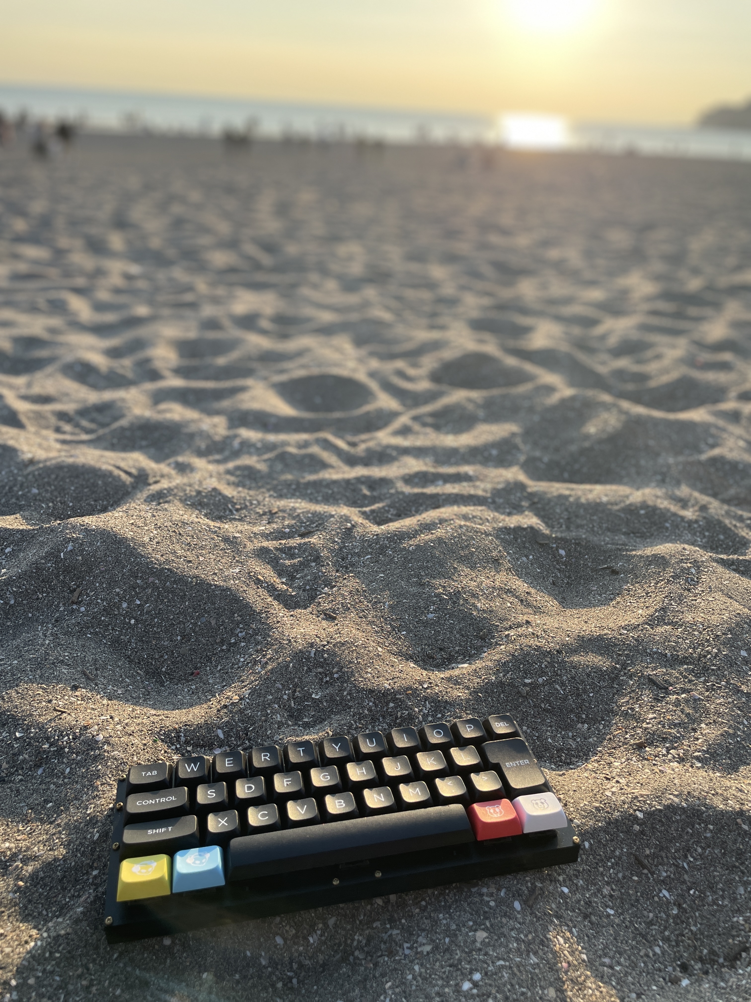
images/build/IMG_3176.jpg
