takashicompany/tightwriter/images/build/IMG_3177.jpg

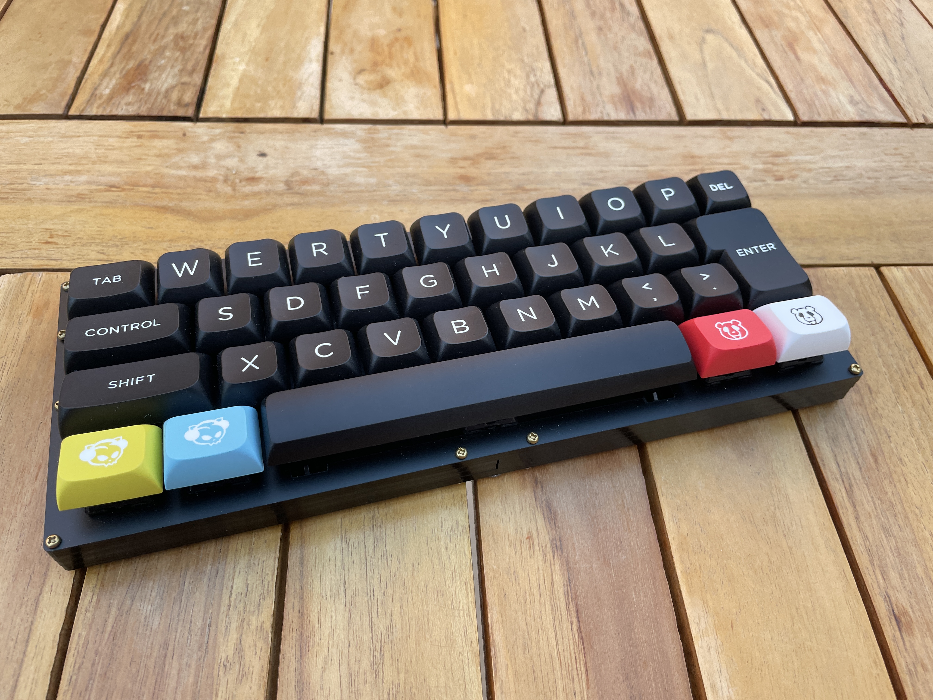
images/build/IMG_3177.jpg
