takashicompany/tightwriter/images/build/IMG_3178.jpg

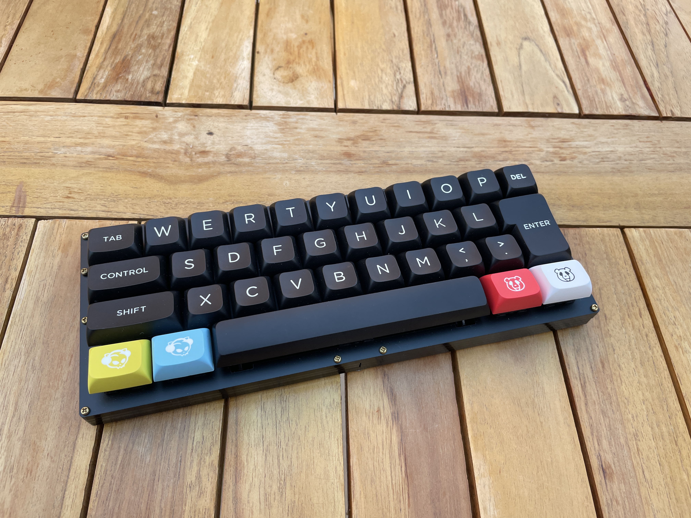
images/build/IMG_3178.jpg
