takashicompany/tightwriter/images/build/IMG_3179.jpg

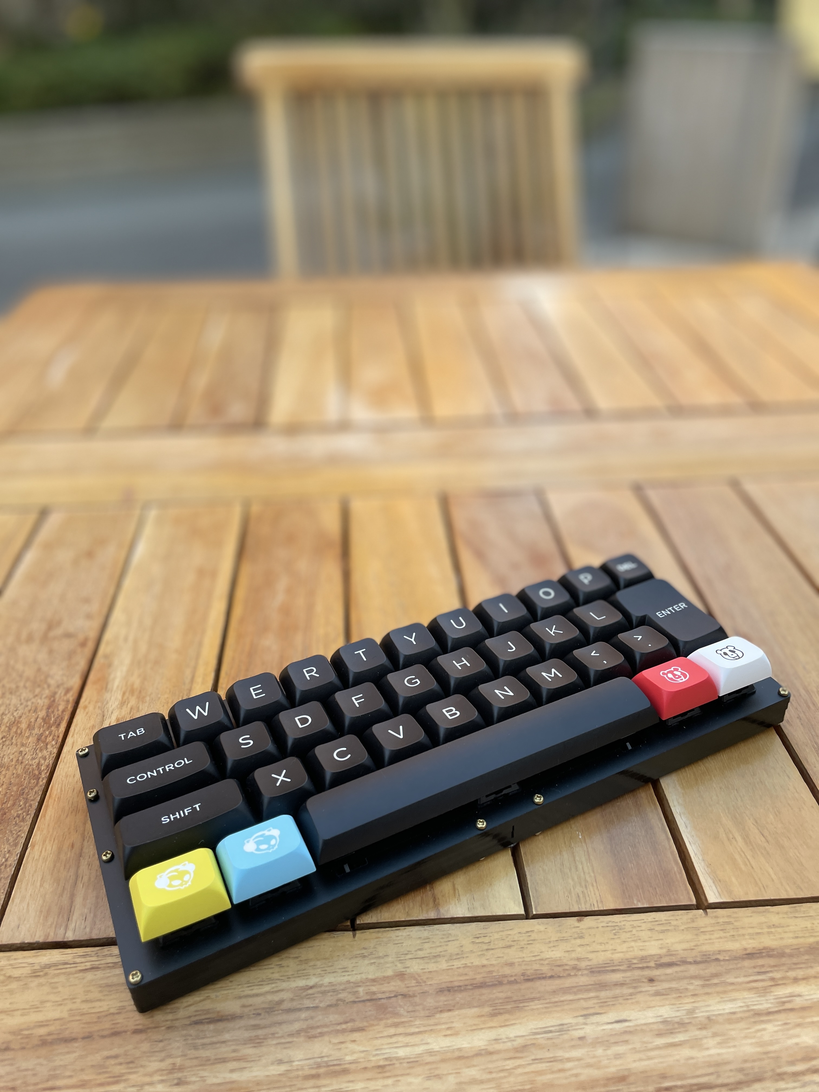
images/build/IMG_3179.jpg
