takashicompany/tightwriter/images/build/IMG_3180.jpg

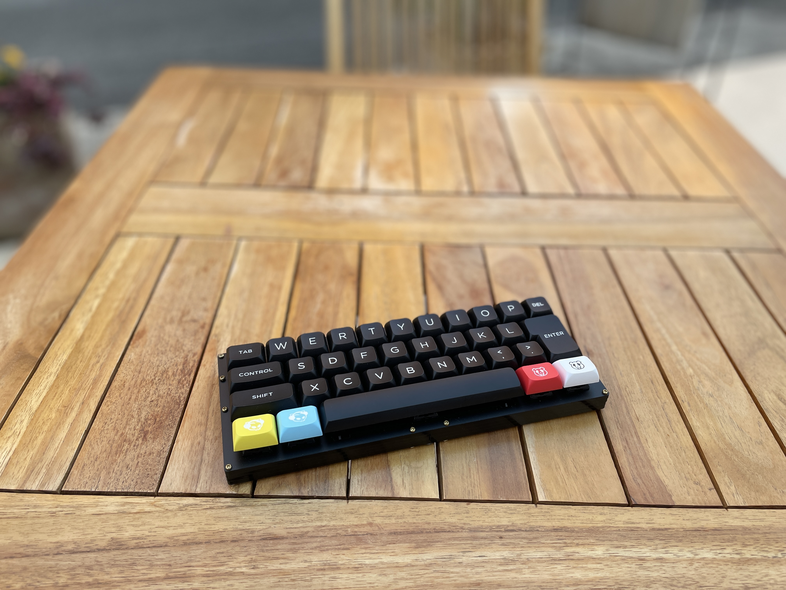
images/build/IMG_3180.jpg
