takashicompany/tightwriter/images/build/IMG_4098.jpg

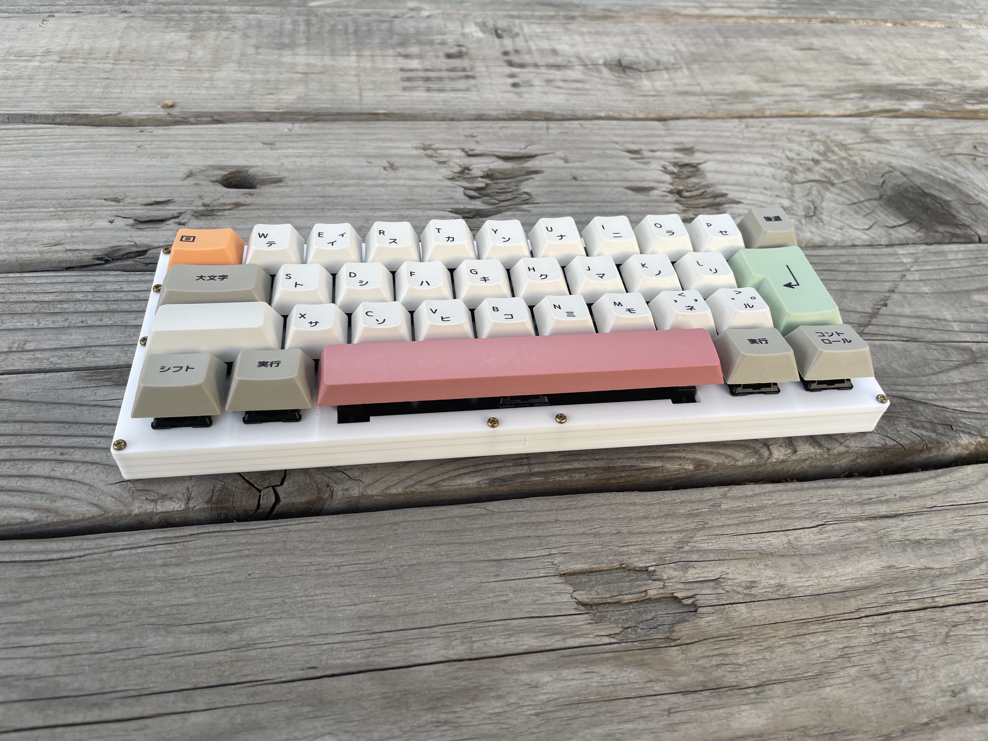
images/build/IMG_4098.jpg
