takashicompany/tightwriter/images/build/IMG_4099.jpg

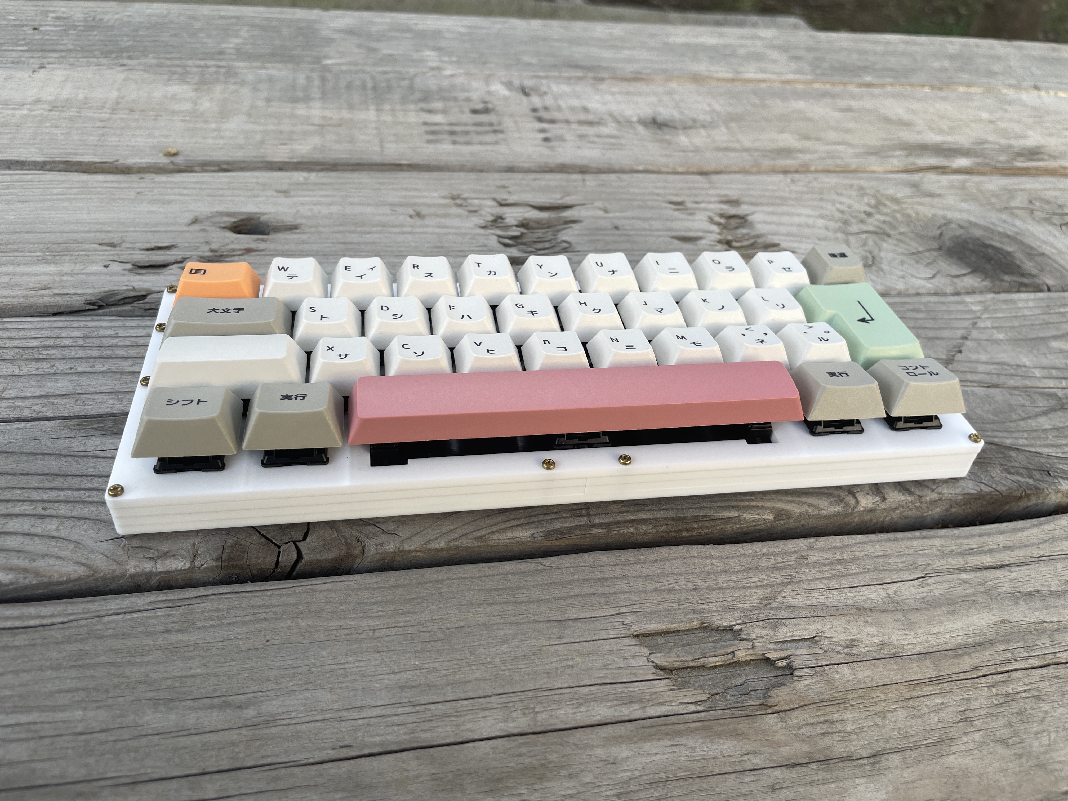
images/build/IMG_4099.jpg
