takashicompany/tightwriter/images/build/IMG_4100.jpg

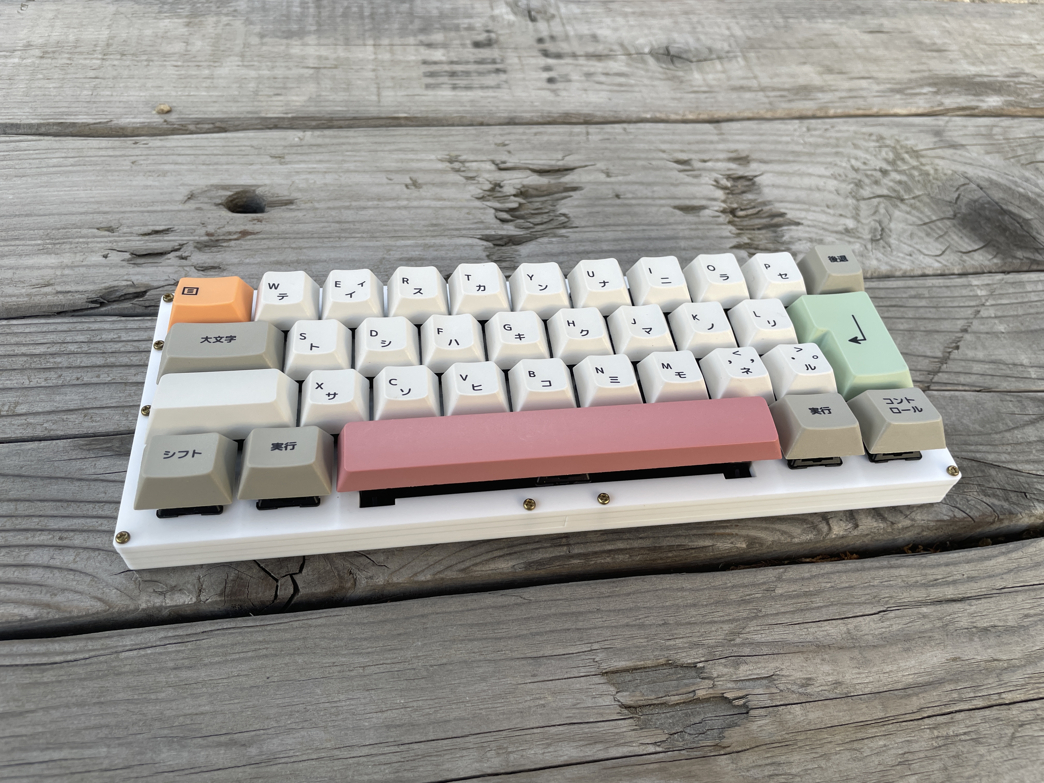
images/build/IMG_4100.jpg
