takashicompany/tightwriter/images/build/IMG_4101.jpg

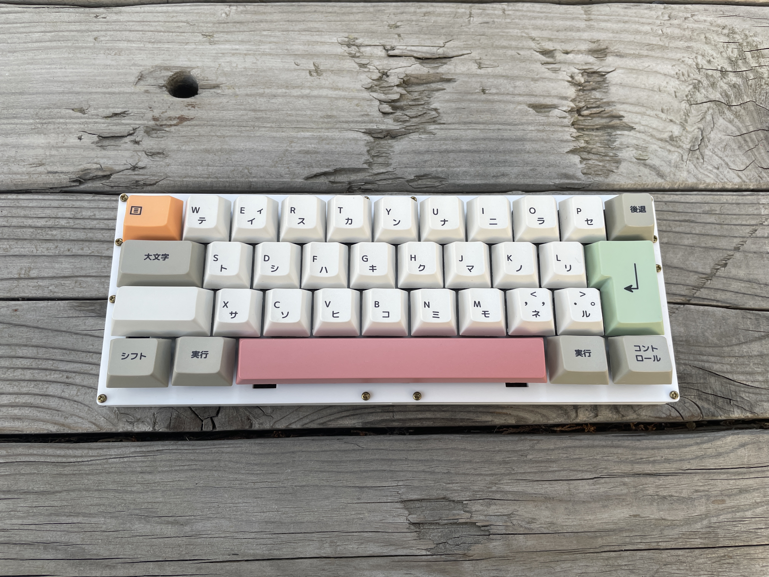
images/build/IMG_4101.jpg
