takashicompany/tightwriter/images/build/IMG_4104.jpg

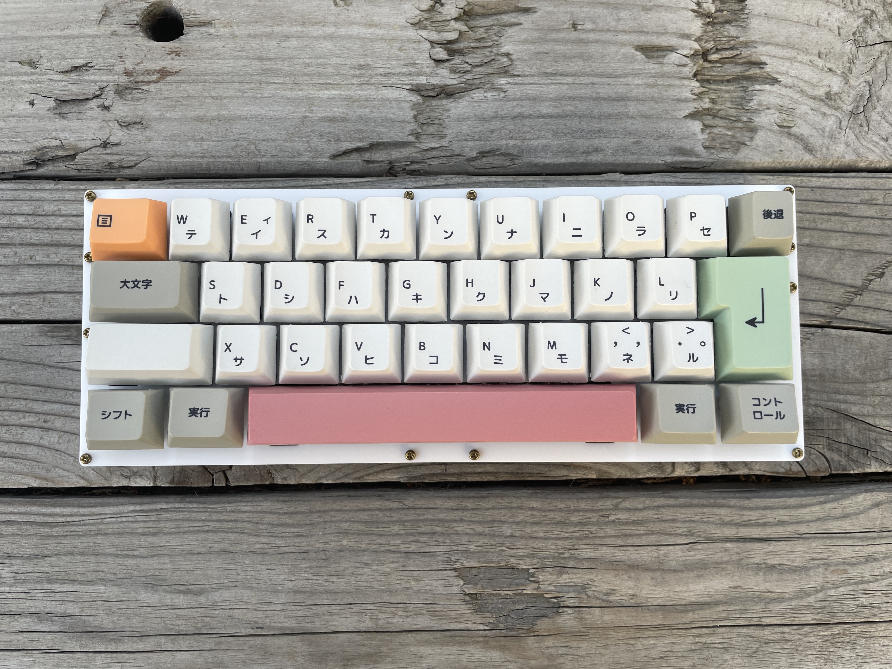
images/build/IMG_4104.jpg
