takashicompany/tightwriter/images/build/IMG_4111.jpg

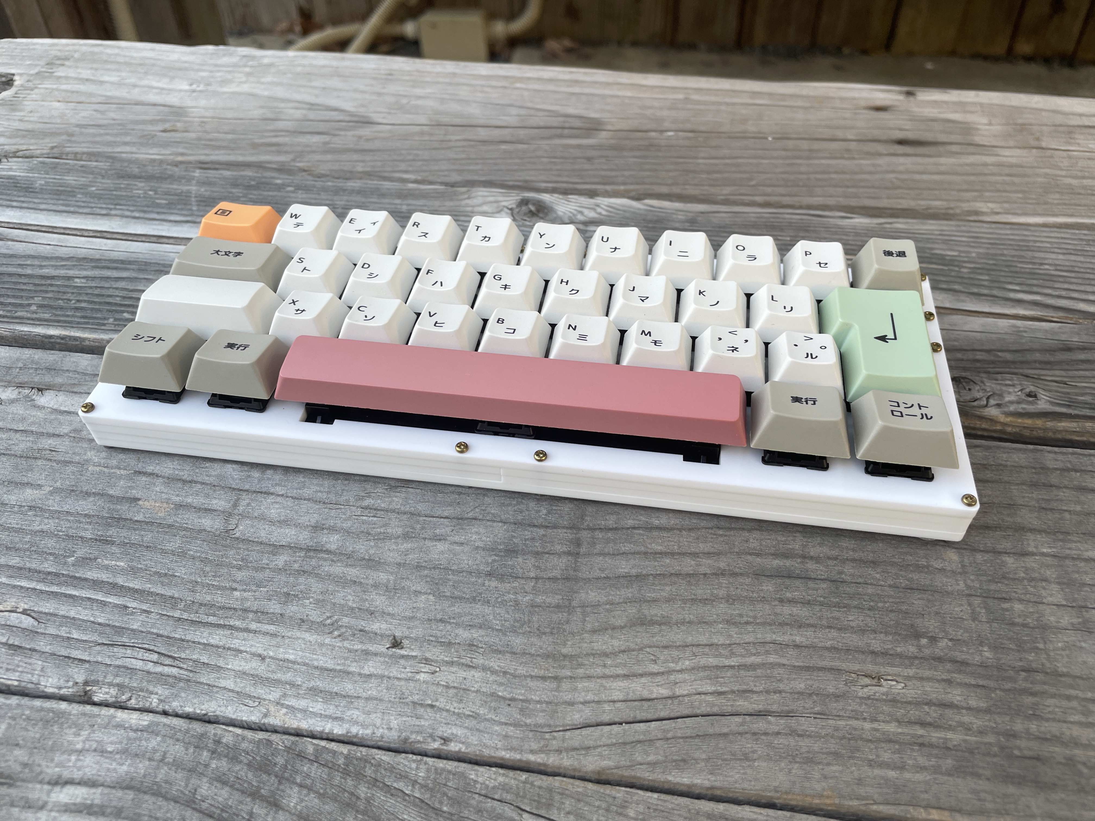
images/build/IMG_4111.jpg
