takashicompany/tightwriter/images/build/IMG_4115.jpg

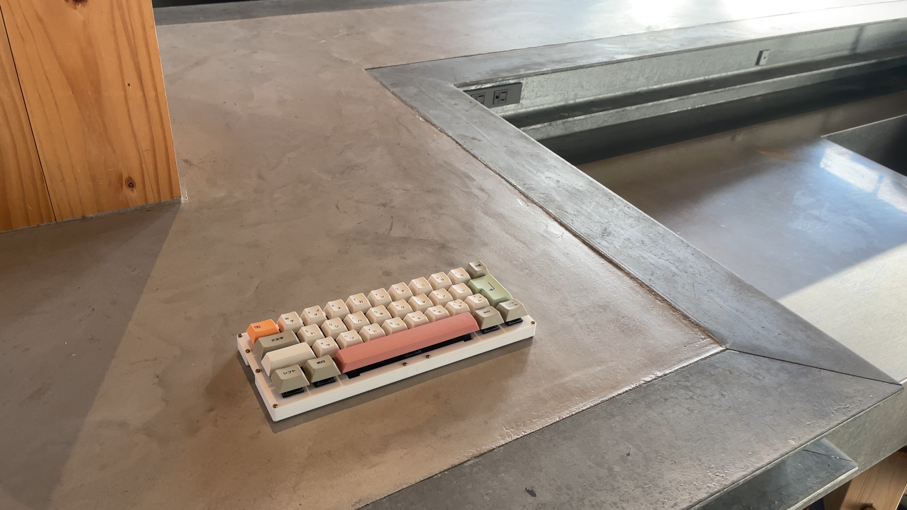
images/build/IMG_4115.jpg
