takashicompany/tightwriter/images/build/IMG_4116.jpg

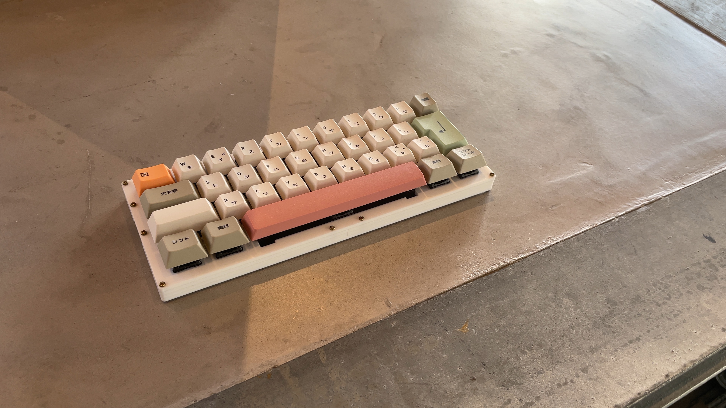
images/build/IMG_4116.jpg
