takashicompany/tightwriter/images/build/IMG_4119.jpg

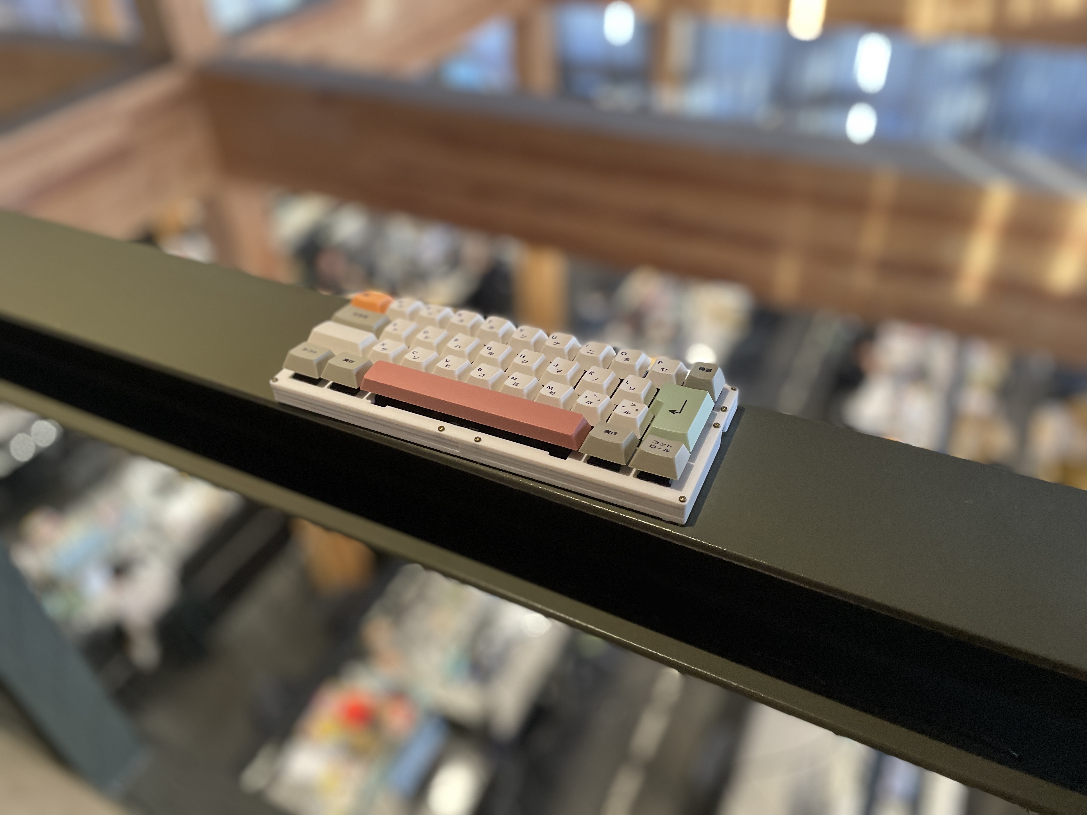
images/build/IMG_4119.jpg
