takashicompany/tightwriter/images/build/IMG_4120.jpg

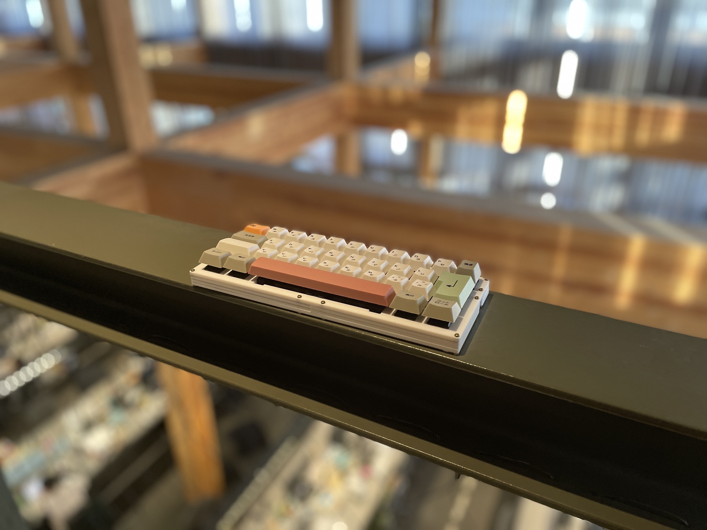
images/build/IMG_4120.jpg
