takashicompany/tightwriter/images/build/IMG_4121.jpg

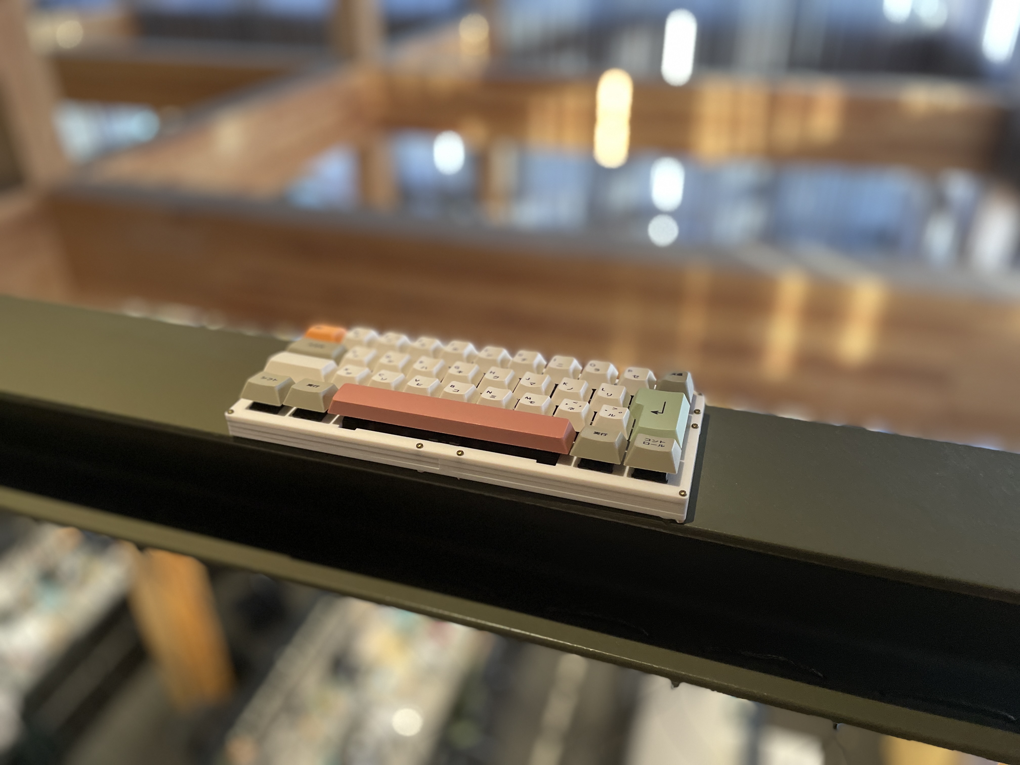
images/build/IMG_4121.jpg
