takashicompany/tightwriter/images/build/IMG_4122.jpg

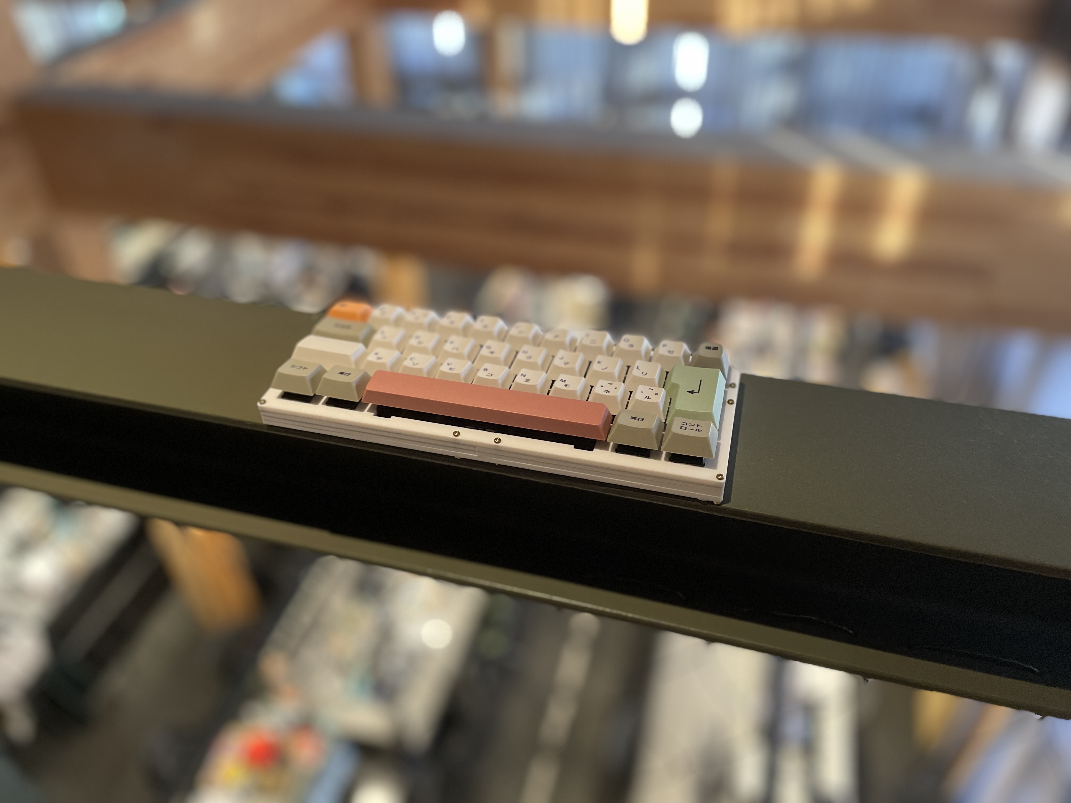
images/build/IMG_4122.jpg
