takashicompany/tightwriter/images/build/IMG_4123.jpg

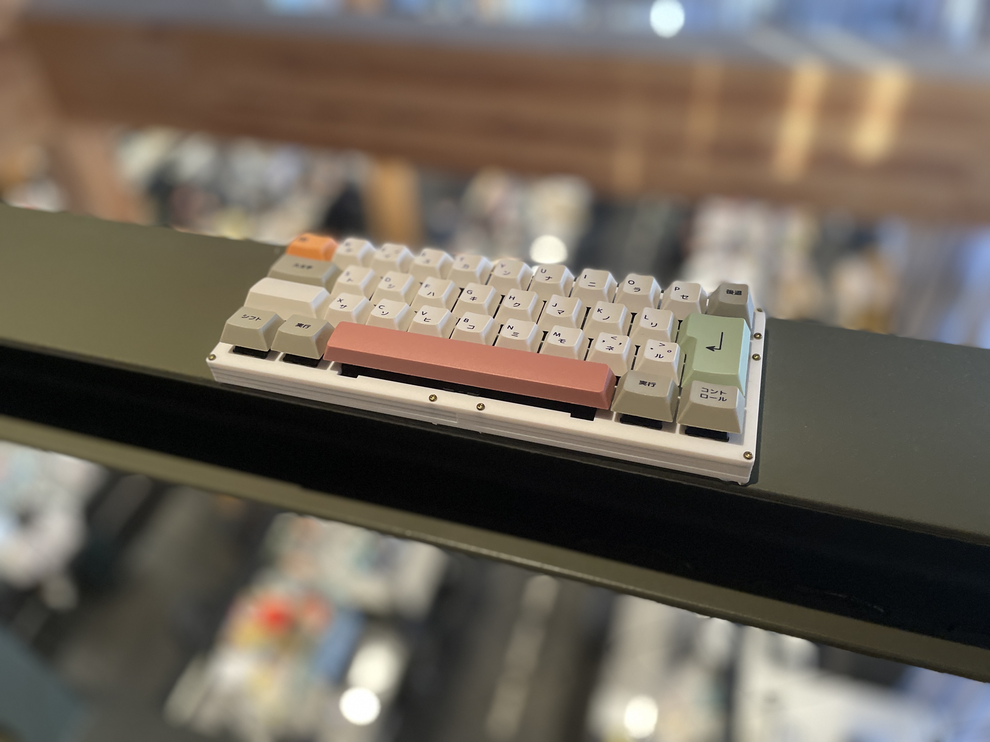
images/build/IMG_4123.jpg
