takashicompany/tightwriter/images/build/IMG_4148.jpg

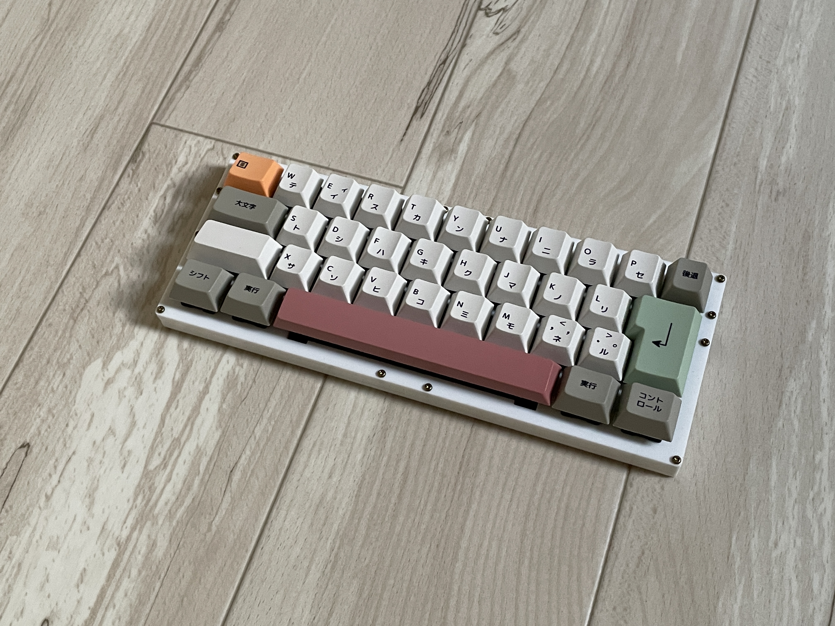
images/build/IMG_4148.jpg
