takashicompany/tightwriter/images/build/IMG_4149.jpg

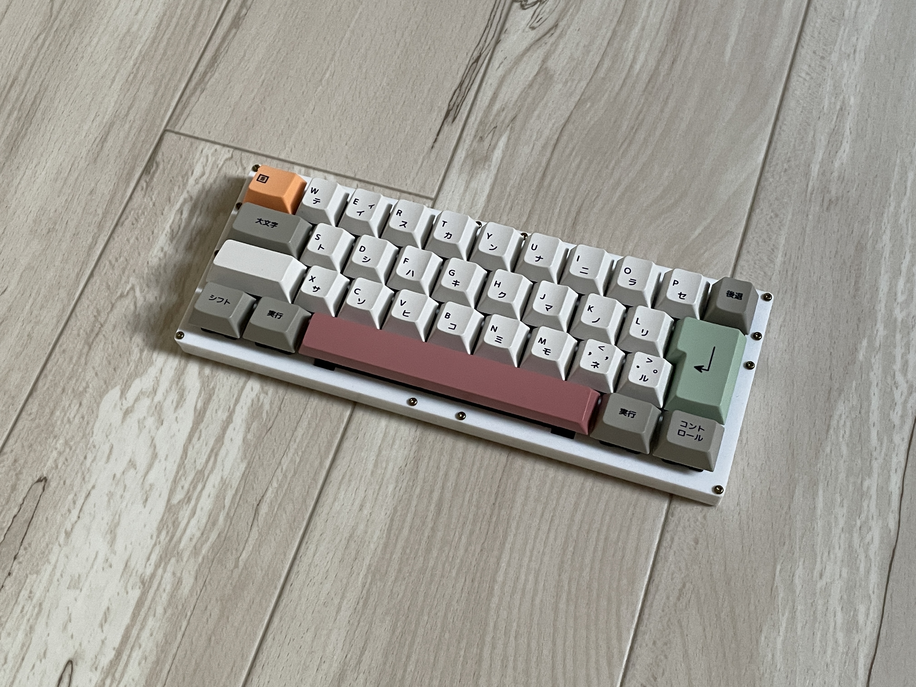
images/build/IMG_4149.jpg
