takashicompany/tightwriter/images/build/IMG_4150.jpg

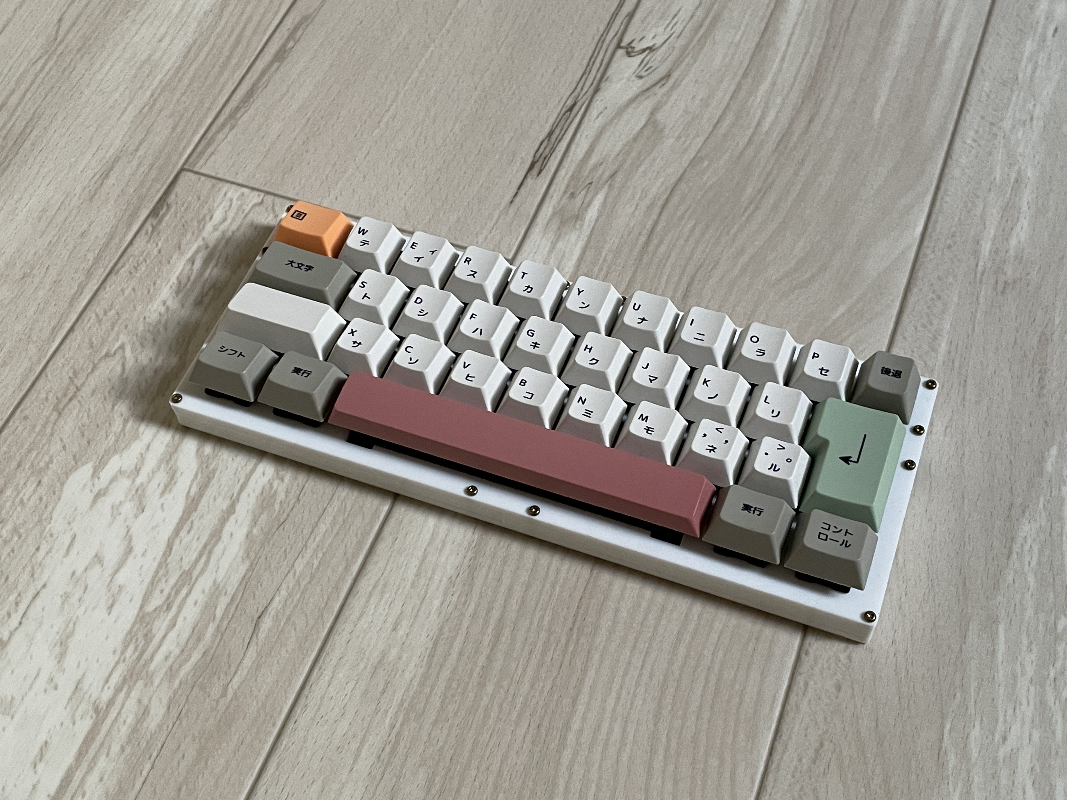
images/build/IMG_4150.jpg
