takashicompany/tightwriter/images/build/IMG_4151.jpg

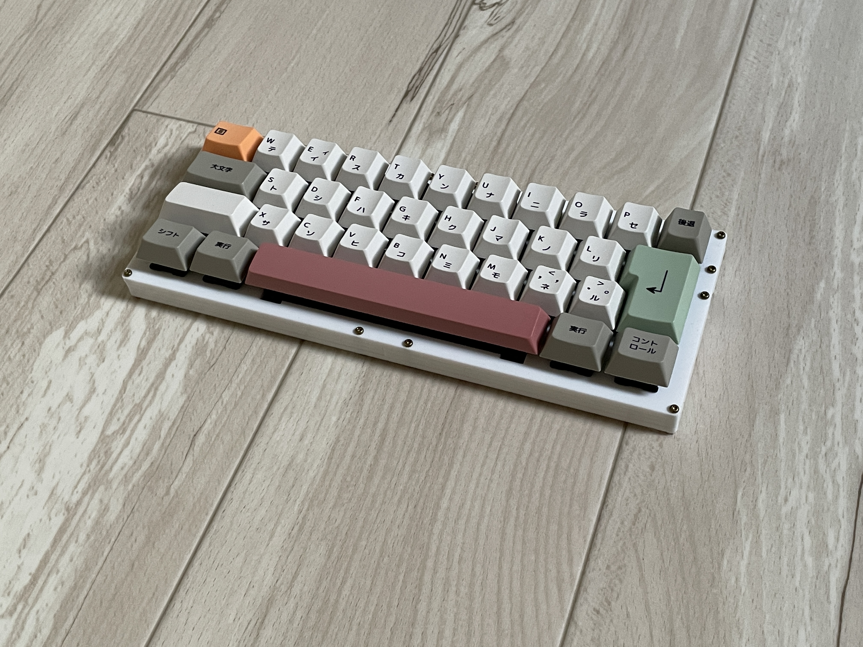
images/build/IMG_4151.jpg
