takashicompany/tightwriter/images/build/IMG_4152.jpg

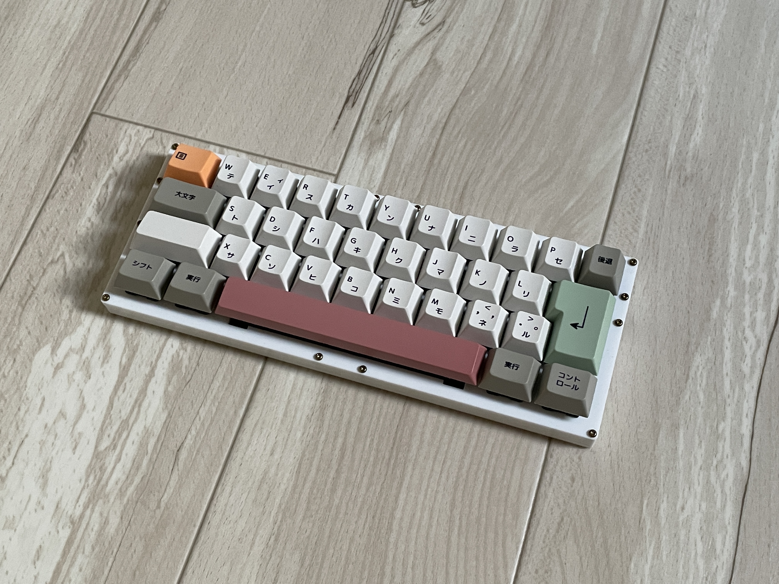
images/build/IMG_4152.jpg
