takashicompany/tightwriter/images/build/IMG_4153.jpg

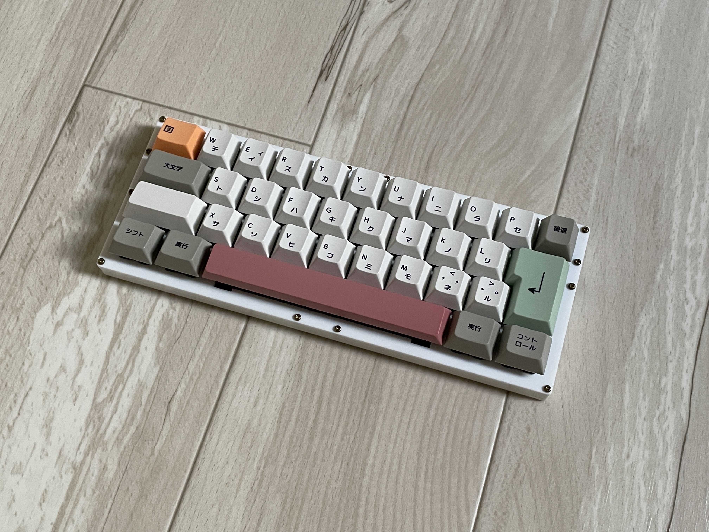
images/build/IMG_4153.jpg
