takashicompany/tightwriter/images/build/IMG_4154.jpg

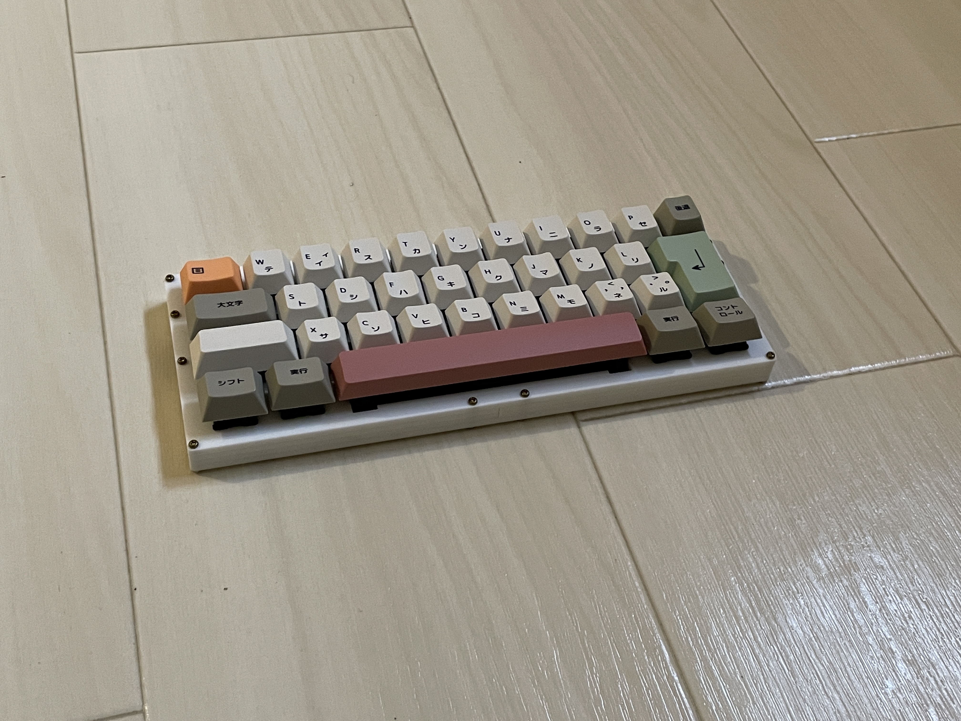
images/build/IMG_4154.jpg
