takashicompany/tightwriter/images/build/IMG_4159.jpg

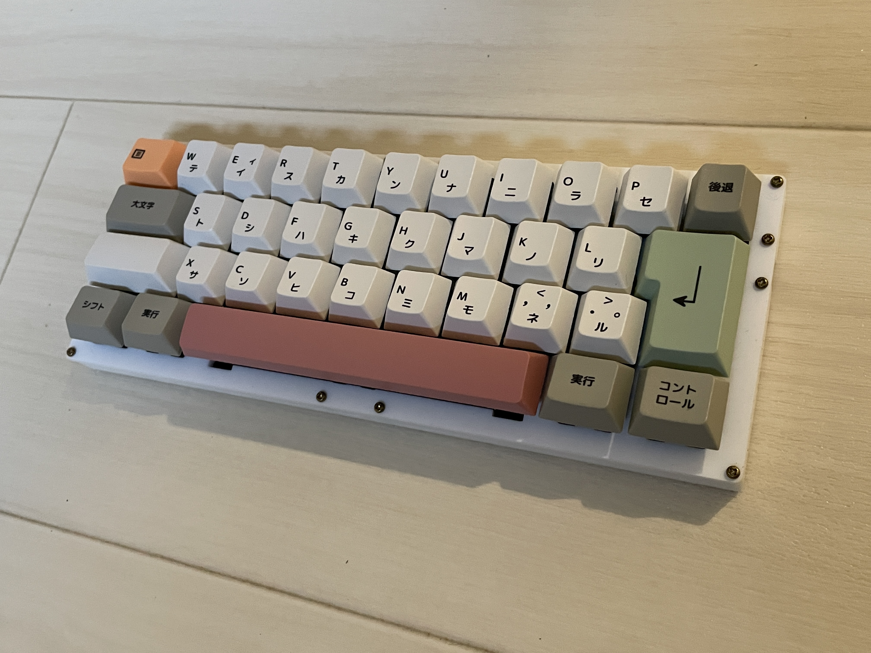
images/build/IMG_4159.jpg
