takashicompany/tightwriter/images/build/IMG_4160.jpg

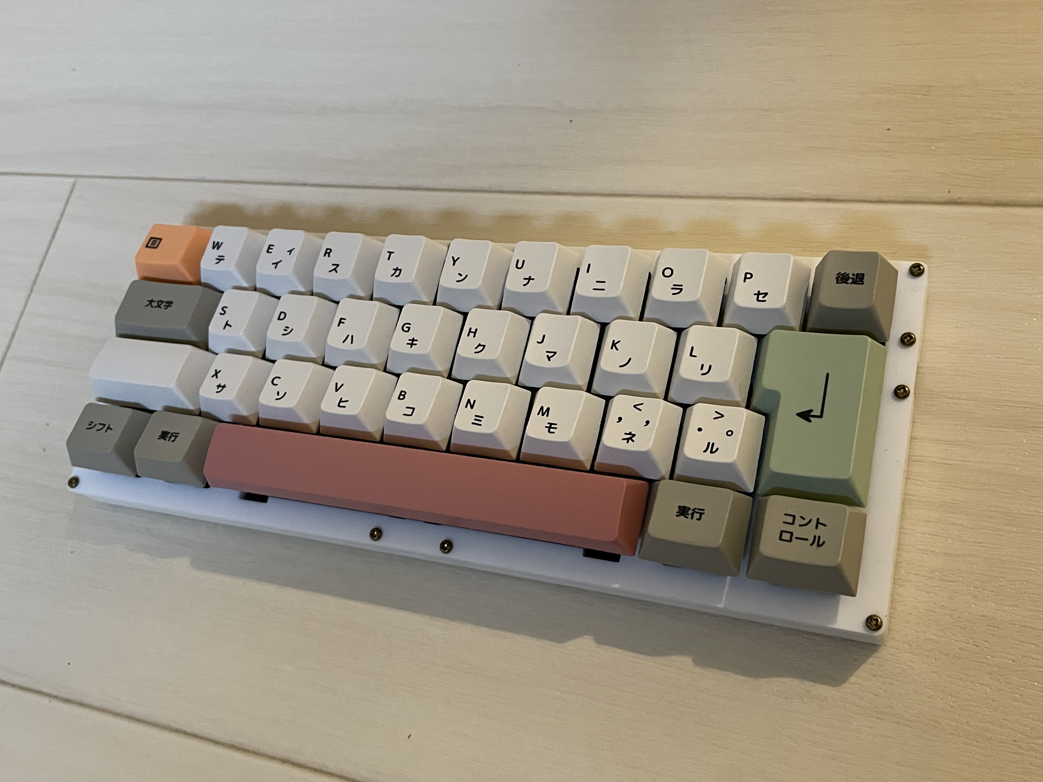
images/build/IMG_4160.jpg
